median-dispersion/GMT-Geiger-Counter/Firmware/GMT-Geiger-Counter/MelodyAlarm.cpp

#include "Melody.h"

const NonBlockingMelody::Note notes[18] = {
  
  {BUZZER_FREQUENCY_HERTZ, 100},
  {0, 50},
  {BUZZER_FREQUENCY_HERTZ, 100},
  {0, 50},
  {BUZZER_FREQUENCY_HERTZ, 100},
  {0, 200},

  {BUZZER_FREQUENCY_HERTZ, 400},
  {0, 50},
  {BUZZER_FREQUENCY_HERTZ, 400},
  {0, 50},
  {BUZZER_FREQUENCY_HERTZ, 400},
  {0, 200},

  {BUZZER_FREQUENCY_HERTZ, 100},
  {0, 50},
  {BUZZER_FREQUENCY_HERTZ, 100},
  {0, 50},
  {BUZZER_FREQUENCY_HERTZ, 100},
  {0, 400}
  
};

Melody MELODY_ALARM = {notes, 18, 1};
