median-dispersion/GMT-Geiger-Counter/Firmware/GMT-Geiger-Counter/ScreenGeigerCounter.cpp

#include "ScreenGeigerCounter.h"

// ------------------------------------------------------------------------------------------------
// Public

// ================================================================================================
// Constructor
// ================================================================================================
ScreenGeigerCounter::ScreenGeigerCounter():

  // Initialize members

  geigerCounterSetting(2, 31, 160, 129),

  audioSettings(          163, 31,  51, 51, IMAGE_VOLUME  ),
  displaySettings(        215, 31,  51, 51, IMAGE_DISPLAY ),
  goToSleep(              267, 31,  51, 51, IMAGE_SLEEP   ),
  decreaseIntegrationTime(163, 83,  51, 51, IMAGE_DECREASE),
  resetIntegrationTime(   215, 83,  51, 51, IMAGE_RESET   ),
  increaseIntegrationTime(267, 83,  51, 51, IMAGE_INCREASE),
  cosmicRayDetector(      163, 135, 51, 51, IMAGE_MUON    ),
  radiationHistory(       215, 135, 51, 51, IMAGE_HISTORY ),
  trueRNG(                267, 135, 51, 51, IMAGE_DICE    ),
  hotspotSettings(        163, 187, 51, 51, IMAGE_HOTSPOT ),
  wifiSettings(           215, 187, 51, 51, IMAGE_WIFI    ),
  systemSettings(         267, 187, 51, 51, IMAGE_SETTINGS),
  
  _equivalentDoseString("0.00"),
  _countsPerMinuteString("0 CPM"),
  _integrationTimeString("30 s"),

  _equivalentDoseScreen(2, 31, 160, 129, COLOR_GREEN_MEDIUM, COLOR_GREEN_DARK, _equivalentDoseString.c_str(), STRING_MICRO_SIEVERTS_PER_HOUR_ABBREVIATION),
  _radiationRating(2, 161, 160, IMAGE_RADIATION, STRING_NORMAL                 ),
  _countsPerMinute(2, 187, 160, IMAGE_PARTICLE,  _countsPerMinuteString.c_str()),
  _integrationTime(2, 213, 160, IMAGE_CLOCK,     _integrationTimeString.c_str())

{}

// ================================================================================================
// Update
// ================================================================================================
void ScreenGeigerCounter::update(const XPT2046::Point &position) {

  // Update screen elements
  audioSettings.update(position);
  displaySettings.update(position);
  goToSleep.update(position);
  decreaseIntegrationTime.update(position);
  resetIntegrationTime.update(position);
  increaseIntegrationTime.update(position);
  cosmicRayDetector.update(position);
  radiationHistory.update(position);
  trueRNG.update(position);
  hotspotSettings.update(position);
  wifiSettings.update(position);
  systemSettings.update(position);
  geigerCounterSetting.update(position);

}

// ================================================================================================
// Draw
// ================================================================================================
void ScreenGeigerCounter::draw(GFXcanvas16 &canvas) {

  // Clear framebuffer
  canvas.fillScreen(COLOR_BLACK);

  // Draw screen border
  canvas.drawRect(0, 29, 320, 211, COLOR_WHITE);

  // Draw title bar
  canvas.drawRect(0, 0, 320, 30, COLOR_WHITE);
  canvas.fillRect(1, 1, 318, 28, COLOR_GRAY_DARK);

  // Draw title text
  canvas.setFont(&FreeSans9pt7b);
  canvas.setTextColor(COLOR_WHITE);
  canvas.setCursor(5, 20);
  canvas.print(STRING_BETA_GAMMA_GMT_GEIGER_COUNTER);

  // Draw screen elements
  audioSettings.draw(canvas);
  displaySettings.draw(canvas);
  goToSleep.draw(canvas);
  decreaseIntegrationTime.draw(canvas);
  resetIntegrationTime.draw(canvas);
  increaseIntegrationTime.draw(canvas);
  cosmicRayDetector.draw(canvas);
  radiationHistory.draw(canvas);
  trueRNG.draw(canvas);
  hotspotSettings.draw(canvas);
  wifiSettings.draw(canvas);
  systemSettings.draw(canvas);
  _equivalentDoseScreen.draw(canvas);
  _radiationRating.draw(canvas);
  _countsPerMinute.draw(canvas);
  _integrationTime.draw(canvas);

}

// ================================================================================================
// Set the equivalent dose
// ================================================================================================
void ScreenGeigerCounter::setEquivalentDose(const double &equivalentDose) {

  // If equivalent dose value is less than 1000
  if (equivalentDose < 1000) {

    // Convert equivalent dose to a string
    _equivalentDoseString = equivalentDose;

  // If equivalent dose value is more than 1000
  } else {

    // Drop decimal places and convert to string
    _equivalentDoseString = (uint64_t)(round(equivalentDose));

  }

}

// ================================================================================================
// Set the equivalent dose unit
// ================================================================================================
void ScreenGeigerCounter::setEquivalentDoseUnit(GeigerCounter::EquivalentDoseUnit equivalentDoseUnit) {

  // Depending on the equivalent dose unit selected
  // Set the equivalent dose unit string

  switch (equivalentDoseUnit) {

    case GeigerCounter::MICRO_SIEVERTS_PER_HOUR: _equivalentDoseScreen.setUnit(STRING_MICRO_SIEVERTS_PER_HOUR_ABBREVIATION); break;
    case GeigerCounter::MILLI_SIEVERTS_PER_HOUR: _equivalentDoseScreen.setUnit(STRING_MILLI_SIEVERTS_PER_HOUR_ABBREVIATION); break;
    case GeigerCounter::SIEVERTS_PER_HOUR:       _equivalentDoseScreen.setUnit(STRING_SIEVERTS_PER_HOUR_ABBREVIATION);       break;

    case GeigerCounter::MICRO_REM_PER_HOUR: _equivalentDoseScreen.setUnit(STRING_MICRO_REM_PER_HOUR_ABBREVIATION); break;
    case GeigerCounter::MILLI_REM_PER_HOUR: _equivalentDoseScreen.setUnit(STRING_MILLI_REM_PER_HOUR_ABBREVIATION); break;
    case GeigerCounter::REM_PER_HOUR:       _equivalentDoseScreen.setUnit(STRING_REM_PER_HOUR_ABBREVIATION);       break;

    case GeigerCounter::MICRO_RONTGEN_PER_HOUR: _equivalentDoseScreen.setUnit(STRING_MICRO_RONTGEN_PER_HOUR_ABBREVIATION); break;
    case GeigerCounter::MILLI_RONTGEN_PER_HOUR: _equivalentDoseScreen.setUnit(STRING_MILLI_RONTGEN_PER_HOUR_ABBREVIATION); break;
    case GeigerCounter::RONTGEN_PER_HOUR:       _equivalentDoseScreen.setUnit(STRING_RONTGEN_PER_HOUR_ABBREVIATION);       break;

    case GeigerCounter::MICRO_GRAY_PER_HOUR: _equivalentDoseScreen.setUnit(STRING_MICRO_GRAY_PER_HOUR_ABBREVIATION); break;
    case GeigerCounter::MILLI_GRAY_PER_HOUR: _equivalentDoseScreen.setUnit(STRING_MILLI_GRAY_PER_HOUR_ABBREVIATION); break;
    case GeigerCounter::GRAY_PER_HOUR:       _equivalentDoseScreen.setUnit(STRING_GRAY_PER_HOUR_ABBREVIATION);       break;

  }

}

// ================================================================================================
// Set the radiation rating
// ================================================================================================
void ScreenGeigerCounter::setRadiationRating(const GeigerCounter::RadiationRating radiationRating) {

  // Depending on the radiation rating
  // Update the dose screen border and background color
  // Update the radiation rating info box value
  
  switch (radiationRating) {

    case GeigerCounter::RATING_NORMAL:
      _equivalentDoseScreen.setBorderColor(COLOR_GREEN_MEDIUM);
      _equivalentDoseScreen.setBackgroundColor(COLOR_GREEN_DARK);
      _radiationRating.setValue(STRING_NORMAL);
    break;

    case GeigerCounter::RATING_ELEVATED:
      _equivalentDoseScreen.setBorderColor(COLOR_LIME_MEDIUM);
      _equivalentDoseScreen.setBackgroundColor(COLOR_LIME_DARK);
      _radiationRating.setValue(STRING_ELEVATED);
    break;

    case GeigerCounter::RATING_MEDIUM:
      _equivalentDoseScreen.setBorderColor(COLOR_YELLOW_MEDIUM);
      _equivalentDoseScreen.setBackgroundColor(COLOR_YELLOW_DARK);
      _radiationRating.setValue(STRING_MEDIUM);
    break;

    case GeigerCounter::RATING_HIGH:
      _equivalentDoseScreen.setBorderColor(COLOR_RED_MEDIUM);
      _equivalentDoseScreen.setBackgroundColor(COLOR_RED_DARK);
      _radiationRating.setValue(STRING_HIGH);
    break;

    case GeigerCounter::RATING_EXTREME:
      _equivalentDoseScreen.setBorderColor(COLOR_RED_MEDIUM);
      _equivalentDoseScreen.setBackgroundColor(COLOR_RED_DARK);
      _radiationRating.setValue(STRING_EXTREME);
    break;

  }

}


// ================================================================================================
// Set the counts per minute
// ================================================================================================
void ScreenGeigerCounter::setCountsPerMinute(const double &countsPerMinute) {

  // Convert counts per minute to a string with unit appended to it
  _countsPerMinuteString  = (uint64_t)(round(countsPerMinute));
  _countsPerMinuteString += " ";
  _countsPerMinuteString += STRING_COUNTS_PER_MINUTE_ABBREVIATION;

}

// ================================================================================================
// Set the integration time
// ================================================================================================
void ScreenGeigerCounter::setIntegrationTime(const uint8_t integrationTime) {
  
  // Convert integration time to a string with unit appended to it
  _integrationTimeString  = integrationTime;
  _integrationTimeString += " ";
  _integrationTimeString += STRING_SECONDS_ABBREVIATION;

}
