median-dispersion/GMT-Geiger-Counter/Firmware/GMT-Geiger-Counter/ImageDiagram.cpp

#include "Graphics.h"

const PROGMEM uint8_t data[] = {

  "F)F)F)F)F)F)F)F)F)F)F)F)F)F)F)F)F)F)F)F)F)F)F)F)F)F)F)F)F)F)F)F)F)F)F)F)"
  "F)F)F)F)F)F)F)F)F)F)F)F)\377\377F)F)F)F)F)F)F)F)F)F)F)F)F)F)F)F)F)F)F)F)"
  "F)F)F)F)F)F)F)F)F)F)F)F)F)F)F)F)F)F)F)F)F)F)F)F)F)F)F)F)F)F)F)F)F)F)F)F)"
  "F)F)F)F)F)F)F)F)F)F)F)F)F)F)F)F)F)F)F)F)F)F)F)F)F)F)F)F)F)F)F)F)F)F)F)F)"
  "F)F)F)F)\377\377F)F)F)F)F)F)F)F)F)F)F)F)F)F)F)F)F)F)F)F)F)F)F)F)F)F)F)F)"
  "F)F)F)F)F)F)F)F)F)F)F)F)F)F)F)F)F)F)F)F)F)F)F)F)F)F)F)F)F)F)F)F)F)F)F)F)"
  "F)F)F)F)F)F)F)F)F)F)F)F)F)F)F)F)F)F)F)F)F)F)F)F)F)F)F)F)F)F)F)F)\377\377"
  "F)F)F)F)F)F)F)F)F)F)F)F)F)F)F)F)F)F)F)F)F)F)F)F)F)F)F)F)F)F)F)F)F)F)F)F)"
  "F)F)F)F)F)F)F)F)F)F)F)F)F)F)F)F)F)F)F)F)F)F)F)F)F)F)F)F)F)F)F)F)F)F)F)F)"
  "F)F)F)F)F)F)F)F)F)F)F)F)F)F)F)F)F)F)F)F)F)F)F)F)\377\377F)F)F)F)F)F)F)F)"
  "F)F)F)F)F)F)F)F)F)F)F)F)F)F)F)F)F)F)F)F)F)F)F)F)F)F)F)F)F)F)F)F)F)F)F)F)"
  "F)F)F)F)F)F)F)F)F)F)F)F)F)F)F)F)F)F)F)F)F)F)F)F)F)F)F)F)F)F)F)F)F)F)F)F)"
  "F)F)F)F)F)F)F)F)F)F)F)F)F)F)F)F)\377\377F)F)F)F)F)F)F)F)F)F)F)F)F)F)F)F)"
  "F)F)F)F)F)F)F)F)F)F)F)F)F)F)F)F)F)F)F)F)F)F)F)F)F)F)F)F)F)F)F)F)F)F)F)F)"
  "F)F)F)F)F)F)F)F)F)F)F)F)F)F)F)F)F)F)F)F)F)F)F)F)F)F)F)F)F)F)F)F)F)F)F)F)"
  "F)F)F)F)F)F)F)F)\377\377F)F)F)F)F)F)F)F)F)F)F)F)F)F)F)F)F)F)F)F)F)F)F)F)"
  "F)F)F)F)F)F)F)F)F)F)F)F)F)F)F)F)F)F)F)F)F)F)F)F)F)F)F)F)F)F)F)F)F)F)F)F)"
  "F)F)F)F)F)F)F)F)F)F)F)F)F)F)F)F)F)F)F)F)F)F)F)F)F)F)F)F)F)F)F)F)F)F)F)F)"
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
  "\265\070\306\314Z\314Z\314Z\314Z\314Z\314Z\314Z\314Z\314Z\314Z\314Z\314Z\314"
  "Z\314Z\314Z\314Z\314Z\314Z\314Z\314Z\314Z\314Z\314Z\314Z\314Z\314Z\314Z\377"
  "\377\377\377\377\377\377\377\377\377\377\377\377\377\323\234F)\323\234\377"
  "\377\314Z\314Z\314Z\314Z\314Z\314Z\377\377\314Z\314Z\314Z\314Z\314Z\314Z"
  "\314Z\314Z\314Z\314Z\314Z\314Z\314Z\314Z\314Z\314Z\314Z\314Z\314Z\314Z\314"
  "Z\314Z\314Z\314Z\314Z\314Z\314Z\222\224\276\367Y\316\314Z\314Z\257s\276\367"
  "\333\336\314Z\314Z\034\347=\347\327\275\314Z\314Z\314Z\337\377\314Z\222\224"
  "\276\367\333\336\314Z\314Z\226\265\070\306\314Z\314Z\314Z\314Z\314Z\314Z\314"
  "Z\314Z\314Z\314Z\314Z\314Z\314Z\314Z\314Z\314Z\314Z\314Z\314Z\314Z\314Z\314"
  "Z\314Z\314Z\314Z\314Z\314Z\377\377\314Z\314Z\314Z\314Z\314Z\314Z\377\377"
  "\323\234\377\377\314Z\314Z\314Z\314Z\314Z\314Z\314Z\377\377\314Z\314Z\314"
  "Z\314Z\314Z\314Z\314Z\314Z\314Z\314Z\314Z\314Z\314Z\314Z\314Z\314Z\314Z\314"
  "Z\314Z\314Z\314Z\314Z\314Z\314Z\314Z\314Z\314Z\222\224\373\336]\357\314Z"
  "\314Z\226\265\272\326\333\336\314Z\216s\236\367\364\234<\347\314Z\314Z\314"
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
  "Z\314Z\314Z\314Z\314Z\314Z\314Z\222\224\373\336Mk<\347\064\245\030\306\222"
  "\224\333\336nk\377\377\377\377\377\377\377\377\373\336\314Z\314Z\337\377"
  "\314Z\222\224\373\336\314Z\216s\236\367\367\275\070\306\314Z\314Z\314Z\314"
  "Z\314Z\314Z\314Z\314Z\314Z\314Z\314Z\314Z\314Z\314Z\314Z\314Z\314Z\314Z\314"
  "Z\314Z\314Z\314Z\314Z\314Z\314Z\314Z\314Z\377\377\314Z\314Z\314Z\314Z\314"
  "Z\314Z\314Z\377\377\323\234\377\377\314Z\314Z\314Z\314Z\314Z\314Z\377\377"
  "\314Z\314Z\314Z\314Z\314Z\314Z\314Z\314Z\314Z\314Z\314Z\314Z\314Z\314Z\314"
  "Z\314Z\314Z\314Z\314Z\314Z\314Z\314Z\314Z\314Z\314Z\314Z\314Z\222\224\373"
  "\336\314Z\373\336\374\336r\214\222\224\333\336v\255\373\336\314Z\314Z\317"
  "{\337\377Nk\314Z\337\377\314Z\222\224\373\336\314Z\314Z\267\265\276\367\070"
  "\306\314Z\314Z\314Z\314Z\314Z\314Z\314Z\314Z\314Z\314Z\314Z\314Z\314Z\314"
  "Z\314Z\314Z\314Z\314Z\314Z\314Z\314Z\314Z\314Z\314Z\314Z\314Z\314Z\377\377"
  "\314Z\314Z\314Z\314Z\314Z\314Z\377\377\323\234\304\030\323\234\377\377\377"
  "\377\377\377\377\377\377\377\377\377\377\377\314Z\314Z\314Z\314Z\314Z\314"
  "Z\314Z\314Z\314Z\314Z\314Z\314Z\314Z\314Z\314Z\314Z\314Z\314Z\314Z\314Z\314"
  "Z\314Z\314Z\314Z\314Z\314Z\314Z\222\224\373\336\314Z\266\265\236\367\314"
  "Z\222\224\333\336\333\336U\255\314Z\314Z\314Z\034\347u\255\314Z\337\377\314"
  "Z\222\224\373\336\314Z\314Z\354Z]\357\070\306\314Z\314Z\314Z\314Z\314Z\314"
  "Z\314Z\314Z\314Z\314Z\314Z\314Z\314Z\314Z\314Z\314Z\314Z\314Z\314Z\314Z\314"
  "Z\314Z\314Z\314Z\314Z\314Z\314Z\377\377\377\377\377\377\377\377\377\377\377"
  "\377\377\377\323\234\304\030\304\030\304\030\304\030\304\030\304\030\304\030\304"
  "\030\304\030\377\377\314Z\314Z\314Z\314Z\314Z\314Z\314Z\314Z\314Z\314Z\314"
  "Z\314Z\314Z\314Z\314Z\314Z\314Z\314Z\314Z\314Z\314Z\314Z\314Z\314Z\314Z\314"
  "Z\314Z\314Z\314Z\314Z\314Z\314Z\314Z\314Z\314Z\314Z\314Z\314Z\314Z\314Z\314"
  "Z\314Z\314Z\314Z\314Z\314Z\314Z\314Z\314Z\314Z\314Z\314Z\314Z\314Z\314Z\314"
  "Z\314Z\314Z\314Z\314Z\314Z\314Z\314Z\314Z\314Z\314Z\314Z\314Z\314Z\314Z\314"
  "Z\314Z\314Z\314Z\314Z\314Z\314Z\314Z\314Z\377\377\304\030\304\030\304\030\304"
  "\030\304\030\304\030\304\030\304\030F)\304\030\304\030\304\030\304\030\304\030\304"
  "\030\304\030\323\234\064\245\314Z\314Z\314Z\314Z\314Z\314Z\314Z\314Z\314Z\314"
  "Z\314Z\314Z\314Z\314Z\314Z\314Z\314Z\314Z\314Z\314Z\314Z\314Z\314Z\314Z\314"
  "Z\314Z\314Z\314Z\314Z\314Z\314Z\314Z\314Z\314Z\314Z\314Z\314Z\314Z\314Z\314"
  "Z\314Z\314Z\314Z\314Z\314Z\314Z\314Z\314Z\314Z\314Z\314Z\314Z\314Z\314Z\314"
  "Z\314Z\314Z\314Z\314Z\314Z\314Z\314Z\314Z\314Z\314Z\314Z\314Z\314Z\314Z\314"
  "Z\314Z\314Z\314Z\314Z\314Z\314Z\314Z\064\245\323\234\304\030\304\030\304\030"
  "\304\030\304\030\304\030\304\030F)F)F)F)F)F)F)F)\304\030\304\030\323\234\377\377"
  "\377\377\377\377\377\377\377\377\377\377\377\377\377\377\377\377\377\377"
  "\377\377\377\377\377\377\377\377\377\377\377\377\377\377\377\377\377\377"
  "\377\377\377\377\377\377\377\377\377\377\377\377\377\377\377\377\377\377"
  "\377\377\377\377\377\377\377\377\377\377\377\377\377\377\377\377\377\377"
  "\377\377\377\377\377\377\377\377\377\377\377\377\377\377\377\377\377\377"
  "\377\377\377\377\377\377\377\377\377\377\377\377\377\377\377\377\377\377"
  "\377\377\377\377\377\377\377\377\377\377\377\377\377\377\377\377\377\377"
  "\377\377\377\377\377\377\377\377\377\377\377\377\377\377\377\377\377\377"
  "\377\377\377\377\377\377\377\377\323\234\304\030\304\030F)F)F)F)F)F)F)F)F)"
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
  "Z\314Z\314Z\314Z\314Z\314Z\314Z\314Z\314Z\314Z\314Z\314Z\314Z\314Z\314Z\314"
  "Z\314Z\314Z\314Z\314Z\314Z\314Z\314Z\314Z\314Z\314Z\314Z\314Z\314Z\314Z\314"
  "Z\314Z\314Z\314Z\314Z\314Z\314Z\314Z\314Z\314Z\314Z\314Z\314Z\064\245\323"
  "\234F)F)F)F)F)F)F)F)F)F)F)F)F)F)F)F)\377\377\314Z\314Z\314Z\314Z\314Z\314"
  "Z\314Z\314Z\314Z\314Z\314Z\314Z\314Z\314Z\314Z\314Z\314Z\314Z\314Z\314Z\314"
  "Z\314Z\314Z\314Z\314Z\314Z\314Z\314Z\314Z\314Z\314Z\314Z\314Z\314Z\314Z\314"
  "Z\314Z\314Z\314Z\314Z\314Z\314Z\314Z\314Z\314Z\314Z\314Z\314Z\314Z\314Z\314"
  "Z\314Z\314Z\314Z\314Z\314Z\314Z\314Z\314Z\314Z\314Z\314Z\314Z\314Z\314Z\314"
  "Z\314Z\314Z\314Z\314Z\314Z\314Z\314Z\314Z\314Z\314Z\314Z\314Z\314Z\377\377"
  "F)F)F)F)F)F)F)F)F)\323\234\377\377\377\377\377\377\377\377\377\377\377\377"
  "\377\377\314Z\314Z\314Z\314Z\314Z\314Z\314Z\314Z\314Z\314Z\314Z\222\224\377"
  "\377\377\377\377\377\377\377\373\336\314Z\317{\333\336\337\377\276\367\232"
  "\326Nk\314Z\222\224\034\347\314Z\314Z\314Z\314Z\222\224\034\347\314Z\314Z\314"
  "Z\314Z\314Z\317{\333\336\337\377\276\367\232\326Nk\314Z\034\347\024\245\314"
  "Z\314Z\276\367\064\245\314Z\314Z\276\367\064\245\377\377\377\377\377\377\377"
  "\377}\357\222\224\377\377\377\377\377\377\337\377Y\316\314Z\314Z\314Z\314"
  "Z\314Z\314Z\314Z\314Z\314Z\314Z\314Z\314Z\314Z\377\377\377\377\377\377\377"
  "\377\377\377\377\377\377\377\323\234F)\323\234\377\377\314Z\314Z\314Z\314"
  "Z\314Z\314Z\377\377\314Z\314Z\314Z\314Z\314Z\314Z\314Z\314Z\314Z\314Z\314"
  "Z\222\224\034\347\314Z\314Z\314Z\314Z\314Z]\357\030\306\217s\320{\232\326\333"
  "\336\314Z\222\224\034\347\314Z\314Z\314Z\314Z\222\224\034\347\314Z\314Z\314"
  "Z\314Z\314Z]\357\030\306\217s\320{\232\326\333\336\314Z\030\306\070\306\314"
  "Zr\214\377\377Y\316\314Z\360{\236\367\222\224\034\347\314Z\314Z\314Z\314Z"
  "\222\224\034\347\314Z\314Z\317{}\357\263\224\314Z\314Z\314Z\314Z\314Z\314"
  "Z\314Z\314Z\314Z\314Z\314Z\314Z\377\377\314Z\314Z\314Z\314Z\314Z\314Z\377"
  "\377\323\234\377\377\314Z\314Z\314Z\314Z\314Z\314Z\314Z\377\377\314Z\314"
  "Z\314Z\314Z\314Z\314Z\314Z\314Z\314Z\314Z\314Z\222\224\034\347\314Z\314Z\314"
  "Z\314Z\065\245\333\336\314Z\314Z\314Z\314Z}\357Q\214\222\224\034\347\314Z\314"
  "Z\314Z\314Z\222\224\034\347\314Z\314Z\314Z\314Z\065\245\333\336\314Z\314Z\314"
  "Z\314Z}\357Q\214\364\234\373\336\314Z\327\275\034\347]\357\314Z\065\245\272"
  "\326\222\224\034\347\314Z\314Z\314Z\314Z\222\224\034\347\314Z\314Z\314Z\272"
  "\326U\255\314Z\314Z\314Z\314Z\314Z\314Z\314Z\314Z\314Z\314Z\314Z\314Z\377"
  "\377\314Z\314Z\314Z\314Z\314Z\314Z\314Z\377\377\377\377\314Z\314Z\314Z\314"
  "Z\314Z\314Z\314Z\377\377\314Z\314Z\314Z\314Z\314Z\314Z\314Z\314Z\314Z\314"
  "Z\314Z\222\224\377\377\377\377\377\377\377\377\222\224\070\306\266\265\314"
  "Z\314Z\314Z\314Zy\316u\255\222\224\034\347\314Z\314Z\314Z\314Z\222\224\034"
  "\347\314Z\314Z\314Z\314Z\070\306\266\265\314Z\314Z\314Z\314Zy\316u\255Mk\276"
  "\367\314Z\333\336\364\234\276\367nk\071\306\266\265\222\224\377\377\377\377"
  "\377\377\377\377\373\336\222\224\034\347\314Z\314Z\317{}\357\020\204\314Z\314"
  "Z\314Z\314Z\314Z\314Z\314Z\314Z\314Z\314Z\314Z\314Z\377\377\314Z\314Z\314"
  "Z\314Z\314Z\314Z\314Z\377\377\377\377\314Z\314Z\314Z\314Z\314Z\314Z\314Z"
  "\377\377\314Z\314Z\314Z\314Z\314Z\314Z\314Z\314Z\314Z\314Z\314Z\222\224\034"
  "\347\314Z\314Z\314Z\314Z\070\306\266\265\314Z\314Z\314Z\314ZY\316v\255\222"
  "\224\034\347\314Z\314Z\314Z\314Z\222\224\034\347\314Z\314Z\314Z\314Z\070\306"
  "\266\265\314Z\314Z\314Z\314ZY\316v\255\314Z]\357\360{\236\367\015c\272\326"
  "\064\245\034\347Q\214\222\224\034\347\314Z\314Z\314Z\314Z\222\224\377\377\377"
  "\377\377\377\377\377z\316\314Z\314Z\314Z\314Z\314Z\314Z\314Z\314Z\314Z\314"
  "Z\314Z\314Z\314Z\377\377\314Z\314Z\314Z\314Z\314Z\314Z\314Z\377\377\377\377"
  "\314Z\314Z\314Z\314Z\314Z\314Z\314Z\377\377\314Z\314Z\314Z\314Z\314Z\314"
  "Z\314Z\314Z\314Z\314Z\314Z\222\224\034\347\314Z\314Z\314Z\314Z\065\245\333"
  "\336\314Z\314Z\314Z\314Z]\357r\214\222\224\034\347\314Z\314Z\314Z\314Z\222"
  "\224\034\347\314Z\314Z\314Z\314Z\065\245\333\336\314Z\314Z\314Z\314Z]\357r"
  "\214\314Zy\316\070\306\034\347\314Zu\255Y\316\236\367\314Z\222\224\034\347\314"
  "Z\314Z\314Z\314Z\222\224\034\347\314Z\314Z\217s~\357\020\204\314Z\314Z\314"
  "Z\314Z\314Z\314Z\314Z\314Z\314Z\314Z\314Z\314Z\377\377\314Z\314Z\314Z\314"
  "Z\314Z\314Z\314Z\377\377\323\234\377\377\314Z\314Z\314Z\314Z\314Z\314Z\377"
  "\377\314Z\314Z\314Z\314Z\314Z\314Z\314Z\314Z\314Z\314Z\314Z\222\224\034\347"
  "\314Z\314Z\314Z\314Z\314Z]\357\030\306\217s\317{\232\326\373\336\314Z\222"
  "\224\034\347\314Z\314Z\314Z\314Z\222\224\034\347\314Z\314Z\314Z\314Z\314Z]"
  "\357\030\306\217s\317{\232\326\373\336\314Z\314ZU\255\276\367\367\275\314"
  "Z\217s\276\367\374\336\314Z\222\224\034\347\314Z\314Z\314Z\314Z\222\224\034"
  "\347\314Z\314Z\314Z\333\336\263\224\314Z\314Z\314Z\314Z\314Z\314Z\314Z\314"
  "Z\314Z\314Z\314Z\314Z\377\377\314Z\314Z\314Z\314Z\314Z\314Z\377\377\323\234"
  "\304\030\323\234\377\377\377\377\377\377\377\377\377\377\377\377\377\377\314"
  "Z\314Z\314Z\314Z\314Z\314Z\314Z\314Z\314Z\314Z\314Z\222\224\034\347\314Z\314"
  "Z\314Z\314Z\314Z\317{\333\336\337\377\337\377\232\326Nk\314Z\222\224\377"
  "\377\377\377\377\377\377\377U\255\222\224\377\377\377\377\377\377\377\377"
  "U\255\314Z\317{\333\336\337\377\337\377\232\326Nk\314Z\314Z\317{\377\377"
  "Q\214\314Z\314Z]\357\030\306\314Z\222\224\377\377\377\377\377\377\377\377"
  "\377\377\263\224\034\347\314Z\314Z\314Zz\316\327\275\314Z\314Z\314Z\314Z\314"
  "Z\314Z\314Z\314Z\314Z\314Z\314Z\314Z\377\377\377\377\377\377\377\377\377"
  "\377\377\377\377\377\323\234\304\030\304\030\304\030\304\030\304\030\304\030\304"
  "\030\304\030\304\030\377\377\314Z\314Z\314Z\314Z\314Z\314Z\314Z\314Z\314Z\314"
  "Z\314Z\314Z\314Z\314Z\314Z\314Z\314Z\314Z\314Z\314Z\314Z\314Z\314Z\314Z\314"
  "Z\314Z\314Z\314Z\314Z\314Z\314Z\314Z\314Z\314Z\314Z\314Z\314Z\314Z\314Z\314"
  "Z\314Z\314Z\314Z\314Z\314Z\314Z\314Z\314Z\314Z\314Z\314Z\314Z\314Z\314Z\314"
  "Z\314Z\314Z\314Z\314Z\314Z\314Z\314Z\314Z\314Z\314Z\314Z\314Z\314Z\314Z\314"
  "Z\314Z\314Z\314Z\314Z\314Z\314Z\314Z\314Z\314Z\377\377\304\030\304\030\304"
  "\030\304\030\304\030\304\030\304\030\304\030F)\304\030\304\030\304\030\304\030\304"
  "\030\304\030\304\030\323\234\064\245\314Z\314Z\314Z\314Z\314Z\314Z\314Z\314Z"
  "\314Z\314Z\314Z\314Z\314Z\314Z\314Z\314Z\314Z\314Z\314Z\314Z\314Z\314Z\314"
  "Z\314Z\314Z\314Z\314Z\314Z\314Z\314Z\314Z\314Z\314Z\314Z\314Z\314Z\314Z\314"
  "Z\314Z\314Z\314Z\314Z\314Z\314Z\314Z\314Z\314Z\314Z\314Z\314Z\314Z\314Z\314"
  "Z\314Z\314Z\314Z\314Z\314Z\314Z\314Z\314Z\314Z\314Z\314Z\314Z\314Z\314Z\314"
  "Z\314Z\314Z\314Z\314Z\314Z\314Z\314Z\314Z\314Z\064\245\323\234\304\030\304"
  "\030\304\030\304\030\304\030\304\030\304\030F)F)F)F)F)F)F)F)\304\030\304\030\323"
  "\234\377\377\377\377\377\377\377\377\377\377\377\377\377\377\377\377\377"
  "\377\377\377\377\377\377\377\377\377\377\377\377\377\377\377\377\377\377"
  "\377\377\377\377\377\377\377\377\377\377\377\377\377\377\377\377\377\377"
  "\377\377\377\377\377\377\377\377\377\377\377\377\377\377\377\377\377\377"
  "\377\377\377\377\377\377\377\377\377\377\377\377\377\377\377\377\377\377"
  "\377\377\377\377\377\377\377\377\377\377\377\377\377\377\377\377\377\377"
  "\377\377\377\377\377\377\377\377\377\377\377\377\377\377\377\377\377\377"
  "\377\377\377\377\377\377\377\377\377\377\377\377\377\377\377\377\377\377"
  "\377\377\377\377\377\377\377\377\377\377\377\323\234\304\030\304\030F)F)F)"
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
  "F)F)F)F)F)F)F)F)F)F)F)F)F)F)F)F)F)F)F)F)F)F)F)F)F)F)F)F)F)F)F)F)F)F)F)F)"
  "F)F)F)F)F)F)F)F)F)F)F)F)F)\313ZF)F)F)F)F)F)F)F)F)F)F)F)F)F)F)F)F)F)F)F)F"
  ")F)F)F)F)F)F)F)F)F)F)F)F)F)F)F)F)F)F)F)F)F)F)F)F)F)F)F)"

};

Image IMAGE_DIAGRAM = {97, 99, (const uint16_t*)(data)};
