median-dispersion/GMT-Geiger-Counter/Firmware/GMT-Geiger-Counter/ImageDice.cpp

#include "Graphics.h"

const PROGMEM uint8_t data[] = {

  "\314Z\314Z\015c\065\245\327\275\370\275\370\275\370\275\370\275\370\275\370"
  "\275\370\275\370\275\370\275\370\275\370\275\370\275\370\275\370\275\370"
  "\275\370\275\370\275\370\275\370\275\370\275\370\275\370\275\370\275\370"
  "\275\370\275\370\275\370\275\327\275\065\245\015c\314Z\314Z\314Z\061\204}\357"
  "\377\377\377\377\377\377\377\377\377\377\377\377\377\377\377\377\377\377"
  "\377\377\377\377\377\377\377\377\377\377\377\377\377\377\377\377\377\377"
  "\377\377\377\377\377\377\377\377\377\377\377\377\377\377\377\377\377\377"
  "\377\377\377\377\377\377\377\377}\357\061\204\314Z\015c}\357\377\377\377\377"
  "\377\377\377\377\377\377\377\377\377\377\377\377\377\377\377\377\377\377"
  "\377\377\377\377\377\377\377\377\377\377\377\377\377\377\377\377\377\377"
  "\377\377\377\377\377\377\377\377\377\377\377\377\377\377\377\377\377\377"
  "\377\377\377\377\377\377\377\377}\357\015c\064\245\377\377\377\377\377\377"
  "\377\377\377\377\377\377\377\377\377\377\377\377\377\377\377\377\377\377"
  "\377\377\377\377\377\377\377\377\377\377\377\377\377\377\377\377\377\377"
  "\377\377\377\377\377\377\377\377\377\377\377\377\377\377\377\377\377\377"
  "\377\377\377\377\377\377\377\377\377\377\024\245\327\275\377\377\377\377\377"
  "\377\377\377\377\377\377\377\377\377\377\377\377\377\377\377\377\377\377"
  "\377\377\377\377\377\377\377\377\377\377\377\377\377\377\377\377\377\377"
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
  "\377\377\377\377\377\377\377\377\377\377\377\377\377\377\377\377\377\377"
  "\377\327\275\327\275\377\377\377\377\377\377\377\377\377\377\377\377\377"
  "\377\377\377\377\377\377\377\377\377\377\377\377\377\377\377\377\377\377"
  "\377\377\377\377\377\377\377\377\377\377\377\377\377\377\377\377\377\377"
  "\377\377\377\377\377\377\377\377\377\377\377\377\377\377\377\377\377\377"
  "\377\377\377\327\275\064\245\377\377\377\377\377\377\377\377\377\377\377\377"
  "\377\377\377\377\377\377\377\377\377\377\377\377\377\377\377\377\377\377"
  "\377\377\377\377\377\377\377\377\377\377\377\377\377\377\377\377\377\377"
  "\377\377\377\377\377\377\377\377\377\377\377\377\377\377\377\377\377\377"
  "\377\377\377\377\024\245\015c}\357\377\377\377\377\377\377\377\377\377\377"
  "\377\377\377\377\377\377\377\377\377\377\377\377\377\377\377\377\377\377"
  "\377\377\377\377\377\377\377\377\377\377\377\377\377\377\377\377\377\377"
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

};

Image IMAGE_DICE = {37, 37, (const uint16_t*)(data)};
