median-dispersion/GMT-Geiger-Counter/Firmware/GMT-Geiger-Counter/ImageMuon.cpp

#include "Graphics.h"

const PROGMEM uint8_t data[] = {

  "\314Z\314Z\314Z\314Z\314Z\314Z\314Z\314Z\314Z\314Z\314Z\314Z\314Z\314Z\354"
  "ZQ\214\065\245\266\265\267\265\266\265\065\245Q\214\354Z\314Z\314Z\314Z\314"
  "Z\314Z\314Z\314Z\314Z\314Z\314Z\314Z\314Z\314Z\314Z\314Z\314Z\314Z\314Z\314"
  "Z\314Z\314Z\314Z\314Z\314Z\314Znk\226\265\034\347\337\377\377\377\377\377"
  "\377\377\377\377\377\377\377\377\377\377\337\377\034\347\226\265nk\314Z\314"
  "Z\314Z\314Z\314Z\314Z\314Z\314Z\314Z\314Z\314Z\314Z\314Z\314Z\314Z\314Z\314"
  "Z\314Z\314Z\314Z\217sY\316\337\377\377\377\377\377\377\377\377\377\377\377"
  "\377\377\377\377\377\377\377\377\377\377\377\377\377\377\377\377\337\377"
  "Y\316\216s\314Z\314Z\314Z\314Z\314Z\314Z\314Z\314Z\314Z\314Z\314Z\314Z\314"
  "Z\314Z\314Z\314Z\314Z\226\265\337\377\377\377\377\377\377\377\377\377\377"
  "\377\377\377\377\377\377\377\377\377\377\377\377\377\377\377\377\377\377"
  "\377\377\377\377\377\377\377\276\367\226\265\314Z\314Z\314Z\314Z\314Z\314"
  "Z\314Z\314Z\314Z\314Z\314Z\314Z\314Z\314Z-c\333\336\377\377\377\377\377\377"
  "\377\377\377\377\377\377\377\377\377\377\377\377\377\377\377\377\377\377"
  "\377\377\377\377\377\377\377\377\377\377\377\377\377\377\377\377\377\377"
  "\272\326-c\314Z\314Z\314Z\314Z\314Z\314Z\314Z\314Z\314Z\314Z\314Znk<\347"
  "\377\377\377\377\377\377\377\377\377\377\377\377\377\377\377\377\377\377"
  "\377\377\377\377\377\377\377\377\377\377\377\377\377\377\377\377\377\377"
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
  "Z\314Z\314Z\314Z\314Z\314Z\314Z\314Z\314Z\314Z\314Z\314Z\314Z\314Z\314Z\314"
  "Z\314Z\314Z\354Z\061\204\064\245\226\265\267\265\226\265\064\245\061\204\354"
  "Z\314Z\314Z\314Z\314Z\314Z\314Z\314Z\314Z\314Z\314Z\314Z\314Z\314Z\314Z"

};

Image IMAGE_MUON = {37, 37, (const uint16_t*)(data)};
