median-dispersion/GMT-Geiger-Counter/Firmware/GMT-Geiger-Counter/ImageDiceSmall.cpp

#include "Graphics.h"

const PROGMEM uint8_t data[] = {

  "\314Z\314Z\314Z\354Znknknknknknknknknknknknknknknknknknknknknk\354Z\314Z"
  "\314Z\314Z\314Znk\333\336\337\377\377\377\377\377\377\377\377\377\377\377"
  "\377\377\377\377\377\377\377\377\377\377\377\377\377\377\377\377\377\377"
  "\377\377\377\377\377\377\377\377\377\377\377\377\377\377\337\377\333\336"
  "nk\314Z\314Z\333\336\377\377\377\377\377\377\377\377\377\377\377\377\377"
  "\377\377\377\377\377\377\377\377\377\377\377\377\377\377\377\377\377\377"
  "\377\377\377\377\377\377\377\377\377\377\377\377\377\377\377\377\377\377"
  "\377\333\336\314Z\354Z\337\377\377\377\377\377\377\377\377\377\377\377\377"
  "\377\377\377\377\377\377\377\377\377\377\377\377\377\377\377\377\377\377"
  "\377\377\377\377\377\377\377\377\377\377\377\377\377\377\377\377\377\377"
  "\377\377\377\337\377\354ZNk\377\377\377\377\377\377\377\377\377\377\377\377"
  "\377\377\377\377\377\377\377\377\377\377\377\377\377\377\377\377\377\377"
  "\377\377\377\377\377\377\377\377\377\377\377\377\377\377\377\377\377\377"
  "\377\377\377\377\377\377NkNk\377\377\377\377\377\377\377\377\377\377\377"
  "\377\377\377\377\377\377\377\377\377\377\377\377\377\377\377\377\377\377"
  "\377\377\377\377\377\377\377\377\377\377\377\377\377\377\377\377\377\377"
  "\377\377\377\377\377\377\377NkNk\377\377\377\377\377\377\377\377\377\377"
  "\377\377\377\377]\357\276\367\377\377\377\377\377\377\377\377\377\377\377"
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
  "\377\377\377\377\377\377\377\377\377\377\377\377\377\377\377\377\377\377"
  "\377\377\337\377\354Z\314Z\333\336\377\377\377\377\377\377\377\377\377\377"
  "\377\377\377\377\377\377\377\377\377\377\377\377\377\377\377\377\377\377"
  "\377\377\377\377\377\377\377\377\377\377\377\377\377\377\377\377\377\377"
  "\377\377\377\377\333\336\314Z\314Znk\333\336\337\377\377\377\377\377\377"
  "\377\377\377\377\377\377\377\377\377\377\377\377\377\377\377\377\377\377"
  "\377\377\377\377\377\377\377\377\377\377\377\377\377\377\377\377\377\377"
  "\377\337\377\333\336nk\314Z\314Z\314Z\314Z\354Znknknknknknknknknknknknkn"
  "knknknknknknknknk\354Z\314Z\314Z\314Z"

};

Image IMAGE_DICE_SMALL = {29, 29, (const uint16_t*)(data)};
