median-dispersion/GMT-Geiger-Counter/Firmware/GMT-Geiger-Counter/ImageDisplay.cpp

#include "Graphics.h"

const PROGMEM uint8_t data[] = {

  "\314Z\314Z\314Z\314Z\314Z\314Z\314Z\314Z\314Z\314Z\314Z\314Z\314Z\314Z\364"
  "\234<\347\364\234\314Z\314Z\314Z\314Z\314Z\314Z\314Z\314Z\314Z\314Z\314Z"
  "\314Z\314Z\314Z\314Z\314Z\314Z\314Z\314Z\314Z\314Z\314Z\314Z\314Z\314Z\314"
  "Z\314Z\364\234\337\377\377\377\377\377\024\245\314Z\314Z\314Z\314Z\314Z\314"
  "Z\314Z\314Z\314Z\314Z\314Z\314Z\314Z\314Z\314Z\314Z\314Z\314Z\314Z\314Z\314"
  "Z\314Z\314Z\314Z\314Z\364\234\337\377\377\377\377\377\377\377\377\377\024"
  "\245\314Z\314Z\314Z\314Z\314Z\314Z\314Z\314Z\314Z\314Z\314Z\314Z\314Z\314"
  "Z\314Z\314Z\314Z\314Z\314Z\314Z\314Z\314Z\314Z\364\234\337\377\377\377\377"
  "\377\377\377\377\377\377\377\377\377\024\245\314Z\314Z\314Z\314Z\314Z\314"
  "Z\314Z\314Z\314Z\314Z\314Z\314Z\314Z\314Z\314ZQ\214\272\326\333\336\333\336"
  "\333\336\333\336\333\336\337\377\377\377\377\377\377\377\377\377\377\377"
  "\377\377\377\377\337\377\333\336\333\336\333\336\333\336\333\336\272\326"
  "Q\214\314Z\314Z\314Z\314Z\314Z\314Z\314Z\314Z\272\326\377\377\377\377\377"
  "\377\377\377\377\377\377\377\377\377\377\377\377\377\377\377\377\377\377"
  "\377\377\377\377\377\377\377\377\377\377\377\377\377\377\377\377\377\377"
  "\377\272\326\314Z\314Z\314Z\314Z\314Z\314Z\314Z\314Z\272\326\377\377\377"
  "\377\377\377\377\377\377\377\377\377\377\377\377\377\377\377\377\377\377"
  "\377\377\377\377\377\377\377\377\377\377\377\377\377\377\377\377\377\377"
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
  "\377\377\377\377\377\377\377\377\377\377\377\377\377\377\377\377\377\377"
  "\377\377\377\377\377\377\377\377\377\377\377\377\377\377\377\377\377\377"
  "\377\272\326\314Z\314Z\314Z\314Z\314Z\314Z\314Z\314ZQ\214\272\326\333\336"
  "\333\336\333\336\333\336\333\336\337\377\377\377\377\377\377\377\377\377"
  "\377\377\377\377\377\377\337\377\333\336\333\336\333\336\333\336\333\336"
  "\272\326Q\214\314Z\314Z\314Z\314Z\314Z\314Z\314Z\314Z\314Z\314Z\314Z\314"
  "Z\314Z\314Z\314Z\364\234\337\377\377\377\377\377\377\377\377\377\377\377"
  "\377\377\024\245\314Z\314Z\314Z\314Z\314Z\314Z\314Z\314Z\314Z\314Z\314Z\314"
  "Z\314Z\314Z\314Z\314Z\314Z\314Z\314Z\314Z\314Z\314Z\314Z\364\234\337\377"
  "\377\377\377\377\377\377\377\377\024\245\314Z\314Z\314Z\314Z\314Z\314Z\314"
  "Z\314Z\314Z\314Z\314Z\314Z\314Z\314Z\314Z\314Z\314Z\314Z\314Z\314Z\314Z\314"
  "Z\314Z\314Z\314Z\364\234\337\377\377\377\377\377\024\245\314Z\314Z\314Z\314"
  "Z\314Z\314Z\314Z\314Z\314Z\314Z\314Z\314Z\314Z\314Z\314Z\314Z\314Z\314Z\314"
  "Z\314Z\314Z\314Z\314Z\314Z\314Z\314Z\314Z\364\234<\347\364\234\314Z\314Z"
  "\314Z\314Z\314Z\314Z\314Z\314Z\314Z\314Z\314Z\314Z\314Z\314Z"

};

Image IMAGE_DISPLAY = {31, 31, (const uint16_t*)(data)};
