median-dispersion/GMT-Geiger-Counter/Firmware/GMT-Geiger-Counter/ImageSettings.cpp

#include "Graphics.h"

const PROGMEM uint8_t data[] = {

  "\314Z\314Z\314Z\314Z\314Z\314Z\314Z\314Z\314Z\314Z\314ZNk\373\336]\357]\357"
  "]\357]\357]\357\373\336Nk\314Z\314Z\314Z\314Z\314Z\314Z\314Z\314Z\314Z\314"
  "Z\314Z\314Z\314Z\314Z\314Z\314Z\314Z\314Z\314Z\314Z\314Z\314Zv\255\377\377"
  "\377\377\377\377\377\377\377\377\377\377\377\377v\255\314Z\314Z\314Z\314"
  "Z\314Z\314Z\314Z\314Z\314Z\314Z\314Z\314Z\314Z\314Z\314Z\314Z\314Z\314Z\314"
  "Z\314Z\314Z\314Z\071\306\377\377\377\377\377\377\377\377\377\377\377\377\377"
  "\377\071\306\314Z\314Z\314Z\314Z\314Z\314Z\314Z\314Z\314Z\314Z\314Z\314Z\314"
  "Z\314Z\314Z\314Z\314Z\314Z\314Z\314Z\314Z\314Z\333\336\377\377\377\377\377"
  "\377\377\377\377\377\377\377\377\377\333\336\314Z\314Z\314Z\314Z\314Z\314"
  "Z\314Z\314Z\314Z\314Z\314Z\314Z\314Z\314Z\314Z\314Z\314Z\314Z\314Z\314Z\314"
  "Z\314Z}\357\377\377\377\377\377\377\377\377\377\377\377\377\377\377}\357"
  "\314Z\314Z\314Z\314Z\314Z\314Z\314Z\314Z\314Z\314Z\314Z\314Z\314Z\314ZU\255"
  "\377\377<\347\226\265-c\314Z\354Z\327\275\377\377\377\377\377\377\377\377"
  "\377\377\377\377\377\377\377\377\377\377\367\275\354Z\314Z-c\226\265<\347"
  "\377\377U\255\314Z\314Z\314Z\314Z\314Znk\276\367\377\377\377\377\377\377"
  "\337\377\272\326}\357\377\377\377\377\377\377\377\377\377\377\377\377\377"
  "\377\377\377\377\377\377\377\377\377~\357\272\326\337\377\377\377\377\377"
  "\377\377\276\367nk\314Z\314Z\314Z\314Zy\316\377\377\377\377\377\377\377\377"
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
  "Z\354Z\327\275\377\377\377\377\377\377\377\377\377\377\377\377\377\377\377"
  "\377\377\377\327\275\354Z\314Z-c\226\265<\347\377\377U\255\314Z\314Z\314"
  "Z\314Z\314Z\314Z\314Z\314Z\314Z\314Z\314Z\314Z\314Z\314Z}\357\377\377\377"
  "\377\377\377\377\377\377\377\377\377\377\377}\357\314Z\314Z\314Z\314Z\314"
  "Z\314Z\314Z\314Z\314Z\314Z\314Z\314Z\314Z\314Z\314Z\314Z\314Z\314Z\314Z\314"
  "Z\314Z\314Z\333\336\377\377\377\377\377\377\377\377\377\377\377\377\377\377"
  "\333\336\314Z\314Z\314Z\314Z\314Z\314Z\314Z\314Z\314Z\314Z\314Z\314Z\314"
  "Z\314Z\314Z\314Z\314Z\314Z\314Z\314Z\314Z\314Z\071\306\377\377\377\377\377"
  "\377\377\377\377\377\377\377\377\377\071\306\314Z\314Z\314Z\314Z\314Z\314"
  "Z\314Z\314Z\314Z\314Z\314Z\314Z\314Z\314Z\314Z\314Z\314Z\314Z\314Z\314Z\314"
  "Z\314Zv\255\377\377\377\377\377\377\377\377\377\377\377\377\377\377v\255"
  "\314Z\314Z\314Z\314Z\314Z\314Z\314Z\314Z\314Z\314Z\314Z\314Z\314Z\314Z\314"
  "Z\314Z\314Z\314Z\314Z\314Z\314Z\314ZNk\373\336]\357]\357]\357]\357]\357\373"
  "\336Mk\314Z\314Z\314Z\314Z\314Z\314Z\314Z\314Z\314Z\314Z\314Z"

};

Image IMAGE_SETTINGS = {31, 31, (const uint16_t*)(data)};
