median-dispersion/GMT-Geiger-Counter/Firmware/GMT-Geiger-Counter/ImageDecrease.cpp

#include "Graphics.h"

const PROGMEM uint8_t data[] = {

  "\314Z\314Z\314Z\314Z\314Z\314Z\314Z\314Z\314Z\314Z\314Z\314Z\314Z\314Z\314"
  "ZMk\024\245\354Z\314Z\314Z\314Z\314Z\314Z\314Z\314Z\314Z\314Z\314Z\314Z\363"
  "\234\216s\314Z\314Z\314Z\314Z\314Z\314Z\314Z\314Z\314Z\314Z\314Z\314Z\314"
  "Z\314Z\226\265\276\367\377\377\327\275\314Z\314Z\314Z\314Z\314Z\314Z\314"
  "Z\314Z\314Z\263\224]\357\377\377\034\347\314Z\314Z\314Z\314Z\314Z\314Z\314"
  "Z\314Z\314Z\314Z\314Z\314Z\222\224<\347\377\377\377\377\377\377\071\306\314"
  "Z\314Z\314Z\314Z\314Z\314Z\314Z\257s\272\326\377\377\377\377\377\377]\357"
  "\314Z\314Z\314Z\314Z\314Z\314Z\314Z\314Z\314Z\314Z\317{\272\326\377\377\377"
  "\377\377\377\377\377\377\377\071\306\314Z\314Z\314Z\314Z\314Z\015c\367\275"
  "\337\377\377\377\377\377\377\377\377\377]\357\314Z\314Z\314Z\314Z\314Z\314"
  "Z\314Z\314Z\015c\367\275\337\377\377\377\377\377\377\377\377\377\377\377\377"
  "\377\071\306\314Z\314Z\314Z\314Z\024\245\236\367\377\377\377\377\377\377\377"
  "\377\377\377\377\377]\357\314Z\314Z\314Z\314Z\314Z\314Z\314Z\024\245\236\367"
  "\377\377\377\377\377\377\377\377\377\377\377\377\377\377\377\377\071\306\314"
  "Z\314Zr\214<\347\377\377\377\377\377\377\377\377\377\377\377\377\377\377"
  "\377\377]\357\314Z\314Z\314Z\314Z\314Zr\214<\347\377\377\377\377\377\377"
  "\377\377\377\377\377\377\377\377\377\377\377\377\377\377\071\306nky\316\377"
  "\377\377\377\377\377\377\377\377\377\377\377\377\377\377\377\377\377\377"
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
  "\314Z\314Z\314Z\314Z\314Z\314Z\314Z\314Z\314Z\314Z\314Z\314Z\314Z\314Z\314"
  "ZMk\364\234\314Z\314Z\314Z\314Z\314Z\314Z\314Z\314Z\314Z\314Z\314Z\314Z\323"
  "\234nk"

};

Image IMAGE_DECREASE = {31, 21, (const uint16_t*)(data)};
