median-dispersion/GMT-Geiger-Counter/Firmware/GMT-Geiger-Counter/ImageHotspot.cpp

#include "Graphics.h"

const PROGMEM uint8_t data[] = {

  "\314Z\314Z\314Z\314Z\314Z\314Z\314Z\314Z\314Z\314Z\015c\363\234\070\306\333"
  "\336<\347]\357<\347\333\336\070\306\363\234\354Z\314Z\314Z\314Z\314Z\314Z"
  "\314Z\314Z\314Z\314Z\314Z\314Z\314Z\314Z\314Z\314Z\314Z\314Z\314Z\257sy\316"
  "\337\377\377\377\377\377\377\377\377\377\377\377\377\377\377\377\377\377"
  "\377\377\276\367y\316\217s\314Z\314Z\314Z\314Z\314Z\314Z\314Z\314Z\314Z\314"
  "Z\314Z\314Z\314Z\314Z\015c\070\306\337\377\377\377\377\377\377\377\034\347y"
  "\316\370\275\226\265\370\275y\316\034\347\377\377\377\377\377\377\337\377"
  "\030\306\015c\314Z\314Z\314Z\314Z\314Z\314Z\314Z\314Z\314Z\314Z\314Z\257s]"
  "\357\377\377\377\377}\357\226\265nk\314Z\314Z\314Z\314Z\314Z\314Z\314Znk"
  "\226\265~\357\377\377\377\377]\357\257s\314Z\314Z\314Z\314Z\314Z\314Z\314"
  "Z\314Z\314Zr\214\276\367\377\377\337\377\267\265\354Z\314Z\314Z\314Z\314"
  "Z\314Z\314Z\314Z\314Z\314Z\314Z\314Z\354Z\267\265\337\377\377\377\236\367"
  "Q\214\314Z\314Z\314Z\314Z\314Z\314Z\314Z\257s\236\367\377\377\236\367r\214"
  "\314Z\314Z\314Z\314Z\314Z\314Z\314Z\314Z\314Z\314Z\314Z\314Z\314Z\314Z\314"
  "ZQ\214\236\367\377\377\276\367\317{\314Z\314Z\314Z\314Z\314Z\015c]\357\377"
  "\377\236\367\257s\314Z\314Z\314Z\314Z\314Z\314Z\015c\061\204\222\224\061\204"
  "\354Z\314Z\314Z\314Z\314Z\314Z\314Z\257s\236\367\377\377]\357\015c\314Z\314"
  "Z\314Z\314Z\070\306\377\377\337\377Q\214\314Z\314Z\314Z\314Z\314Z\263\224"
  "\373\336\337\377\377\377\377\377\377\377\337\377\373\336\263\224\314Z\314"
  "Z\314Z\314Z\314Zr\214\337\377\377\377\030\306\314Z\314Z\314Z\257s\337\377"
  "\377\377\267\265\314Z\314Z\314Z\314Z\015c\272\326\377\377\377\377\377\377"
  "\377\377\337\377\377\377\377\377\377\377\377\377\272\326\015c\314Z\314Z\314"
  "Z\314Z\327\275\377\377\337\377\216s\314Z\314Zy\316\377\377}\357\354Z\314"
  "Z\314Z\314Z\015c<\347\377\377\377\377\333\336\363\234\015c\314Z\015c\364\234"
  "\333\336\377\377\377\377<\347\015c\314Z\314Z\314Z\354Z\236\367\377\377y\316"
  "\314Z\015c\276\367\377\377\226\265\314Z\314Z\314Z\314Z\272\326\377\377\337"
  "\377\065\245\314Z\314Z\314Z\314Z\314Z\314Z\314Z\065\245\337\377\377\377\272"
  "\326\314Z\314Z\314Z\314Z\226\265\377\377\276\367\354Z\363\234\377\377\377"
  "\377nk\314Z\314Z\314Z\263\224\377\377\377\377\065\245\314Z\314Z\314Z\314Z"
  "\314Z\314Z\314Z\314Z\314ZU\255\377\377\377\377\263\224\314Z\314Z\314Znk\377"
  "\377\377\377\323\234\070\306\377\377\034\347\314Z\314Z\314Z\314Z\373\336\377"
  "\377\333\336\314Z\314Z\314Z\314Z\314Z\314Z\314Z\314Z\314Z\314Z\314Z\373\336"
  "\377\377\333\336\314Z\314Z\314Z\314Z\034\347\377\377\030\306\333\336\377\377"
  "y\316\314Z\314Z\314Z\015c\337\377\377\377\363\234\314Z\314Z\314Z\314Z\226"
  "\265\272\326\226\265\314Z\314Z\314Z\314Z\364\234\377\377\337\377\015c\314"
  "Z\314Z\314Zy\316\377\377\333\336<\347\377\377\370\275\314Z\314Z\314Z\020\204"
  "\377\377\377\377\015c\314Z\314Z\314Z\226\265\377\377\377\377\377\377\226\265"
  "\314Z\314Z\314Z-c\377\377\377\377\020\204\314Z\314Z\314Z\370\275\377\377<"
  "\347]\357\377\377\226\265\314Z\314Z\314Z\262\224\377\377\337\377\314Z\314"
  "Z\314Z\314Z\272\326\377\377\377\377\377\377\272\326\314Z\314Z\314Z\314Z\337"
  "\377\377\377\222\224\314Z\314Z\314Z\226\265\377\377]\357\373\336\377\377"
  "\370\275\314Z\314Z\314Z\020\204\377\377\377\377-c\314Z\314Z\314Z\226\265\377"
  "\377\377\377\377\377\226\265\314Z\314Z\314Z-c\377\377\377\377\020\204\314"
  "Z\314Z\314Z\370\275\377\377<\347\232\326\377\377y\316\314Z\314Z\314Z\354"
  "Z\337\377\377\377\024\245\314Z\314Z\314Z\314Z\226\265\272\326\226\265\314"
  "Z\314Z\314Z\314Z\024\245\377\377\337\377\354Z\314Z\314Z\314Zz\316\377\377"
  "\273\326\030\306\377\377<\347\314Z\314Z\314Z\314Z\333\336\377\377\373\336"
  "\314Z\314Z\314Z\314Z\314Z\314Z\314Z\314Z\314Z\314Z\314Z\374\336\377\377\333"
  "\336\314Z\314Z\314Z\314Z<\347\377\377\370\275r\214\377\377\377\377\216s\314"
  "Z\314Z\314Z\222\224\377\377\377\377u\255\314Z\314Z\314Z\314Z\314Z\314Z\314"
  "Z\314Z\314Zv\255\377\377\377\377\222\224\314Z\314Z\314Z\217s\377\377\377"
  "\377r\214\314Z\236\367\377\377\266\265\314Z\314Z\314Z\314Z\232\326\377\377"
  "\337\377\217s\314Z\314Z\314Z\314Z\314Z\314Z\314Z\257s\337\377\377\377\232"
  "\326\314Z\314Z\314Z\314Z\267\265\377\377\236\367\314Z\314ZY\316\377\377\236"
  "\367\015c\314Z\314Z\314Z\015c\034\347}\357-c\314Z\314Z\314Z\314Z\314Z\314Z\314"
  "ZMk}\357\034\347\015c\314Z\314Z\314Z\015c\236\367\377\377\071\306\314Z\314Zn"
  "k\337\377\377\377\367\275\314Z\314Z\314Z\314Z\314Z\314Z\314Z\314Z\314Z\314"
  "Z\314Z\314Z\314Z\314Z\314Z\314Z\314Z\314Z\314Z\314Z\314Z\370\275\377\377"
  "\337\377nk\314Z\314Z\314Z\370\275\377\377\377\377\323\234\314Z\314Z\314Z"
  "\314Z\314Z\314Z\314Z\314Z\314Z\314Z\314Z\314Z\314Z\314Z\314Z\314Z\314Z\314"
  "Z\314Z\263\224\337\377\377\377\367\275\314Z\314Z\314Z\314Z\354Z]\357\377"
  "\377\276\367\317{\314Z\314Z\314Z\314Z\314Z\314Z\314Z\314Z\314Z\314Z\314Z"
  "\314Z\314Z\314Z\314Z\314Z\314Z\317{\276\367\377\377]\357\354Z\314Z\314Z\314"
  "Z\314Z\314Z\360{\276\367\377\377\070\306\314Z\314Z\314Z\314Z\314Z\314Z\314"
  "Z\314Z\314Z\314Z\314Z\314Z\314Z\314Z\314Z\314Z\314Z\070\306\377\377\236\367"
  "\360{\314Z\314Z\314Z\314Z\314Z\314Z\314Z\061\204y\316\360{\314Z\314Z\314Z"
  "\314Z\314Z\314Z\314Z\314Z\314Z\314Z\314Z\314Z\314Z\314Z\314Z\314Z\314Z\360"
  "{y\316\061\204\314Z\314Z\314Z\314Z"

};

Image IMAGE_HOTSPOT = {31, 27, (const uint16_t*)(data)};
