median-dispersion/GMT-Geiger-Counter/Firmware/GMT-Geiger-Counter/ImageIncrease.cpp

#include "Graphics.h"

const PROGMEM uint8_t data[] = {

  "\216s\363\234\314Z\314Z\314Z\314Z\314Z\314Z\314Z\314Z\314Z\314Z\314Z\354"
  "Z\024\245Mk\314Z\314Z\314Z\314Z\314Z\314Z\314Z\314Z\314Z\314Z\314Z\314Z\314"
  "Z\314Z\314Z\034\347\377\377]\357\263\224\314Z\314Z\314Z\314Z\314Z\314Z\314"
  "Z\314Z\314Z\327\275\377\377\276\367\226\265\314Z\314Z\314Z\314Z\314Z\314"
  "Z\314Z\314Z\314Z\314Z\314Z\314Z\314Z\314Z]\357\377\377\377\377\377\377\373"
  "\336\360{\314Z\314Z\314Z\314Z\314Z\314Z\314Z\071\306\377\377\377\377\377\377"
  "]\357\263\224\314Z\314Z\314Z\314Z\314Z\314Z\314Z\314Z\314Z\314Z\314Z\314"
  "Z]\357\377\377\377\377\377\377\377\377\337\377\071\306-c\314Z\314Z\314Z\314"
  "Z\314Z\071\306\377\377\377\377\377\377\377\377\377\377\373\336\360{\314Z\314"
  "Z\314Z\314Z\314Z\314Z\314Z\314Z\314Z\314Z]\357\377\377\377\377\377\377\377"
  "\377\377\377\377\377\236\367v\255\314Z\314Z\314Z\314Z\071\306\377\377\377"
  "\377\377\377\377\377\377\377\377\377\337\377\071\306-c\314Z\314Z\314Z\314"
  "Z\314Z\314Z\314Z\314Z]\357\377\377\377\377\377\377\377\377\377\377\377\377"
  "\377\377\377\377=\347\222\224\314Z\314Z\071\306\377\377\377\377\377\377\377"
  "\377\377\377\377\377\377\377\377\377\236\367v\255\314Z\314Z\314Z\314Z\314"
  "Z\314Z\314Z]\357\377\377\377\377\377\377\377\377\377\377\377\377\377\377"
  "\377\377\377\377\377\377\272\326\257s\071\306\377\377\377\377\377\377\377"
  "\377\377\377\377\377\377\377\377\377\377\377\377\377]\357\222\224\314Z\314"
  "Z\314Z\314Z\314Z]\357\377\377\377\377\377\377\377\377\377\377\377\377\377"
  "\377\377\377\377\377\377\377\377\377\337\377]\357\377\377\377\377\377\377"
  "\377\377\377\377\377\377\377\377\377\377\377\377\377\377\377\377\377\377"
  "\232\326\257s\314Z\314Z\314Z]\357\377\377\377\377\377\377\377\377\377\377"
  "\377\377\377\377\377\377\377\377\377\377\377\377\377\377\377\377\377\377"
  "\377\377\377\377\377\377\377\377\377\377\377\377\377\377\377\377\377\377"
  "\377\377\377\377\377\377\337\377\030\306\015c\314Z]\357\377\377\377\377\377"
  "\377\377\377\377\377\377\377\377\377\377\377\377\377\377\377\377\377\377"
  "\377\377\377\377\377\377\377\377\377\377\377\377\377\377\377\377\377\377"
  "\377\377\377\377\377\377\377\377\377\377\377\377\377\377\377~\357\263\224"
  "]\357\377\377\377\377\377\377\377\377\377\377\377\377\377\377\377\377\377"
  "\377\377\377\377\377\377\377\377\377\377\377\377\377\377\377\377\377\377"
  "\377\377\377\377\377\377\377\377\377\377\377\377\377\377\377\377\377\377"
  "\377\377\377\377\377\034\347]\357\377\377\377\377\377\377\377\377\377\377"
  "\377\377\377\377\377\377\377\377\377\377\377\377\377\377\377\377\377\377"
  "\377\377\377\377\377\377\377\377\377\377\377\377\377\377\377\377\377\377"
  "\377\377\377\377\377\377\377\377\377\377~\357\263\224]\357\377\377\377\377"
  "\377\377\377\377\377\377\377\377\377\377\377\377\377\377\377\377\377\377"
  "\377\377\377\377\377\377\377\377\377\377\377\377\377\377\377\377\377\377"
  "\377\377\377\377\377\377\377\377\377\377\377\377\337\377\030\306\015c\314Z"
  "]\357\377\377\377\377\377\377\377\377\377\377\377\377\377\377\377\377\377"
  "\377\377\377\377\377\337\377]\357\377\377\377\377\377\377\377\377\377\377"
  "\377\377\377\377\377\377\377\377\377\377\377\377\377\377\232\326\257s\314"
  "Z\314Z\314Z]\357\377\377\377\377\377\377\377\377\377\377\377\377\377\377"
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
  "Z\314Z\314Znk\323\234\314Z\314Z\314Z\314Z\314Z\314Z\314Z\314Z\314Z\314Z\314"
  "Z\314Z\364\234Mk\314Z\314Z\314Z\314Z\314Z\314Z\314Z\314Z\314Z\314Z\314Z\314"
  "Z\314Z\314Z\314Z"

};

Image IMAGE_INCREASE = {31, 21, (const uint16_t*)(data)};
