median-dispersion/GMT-Geiger-Counter/Firmware/GMT-Geiger-Counter/ImagePower.cpp

#include "Graphics.h"

const PROGMEM uint8_t data[] = {

  "@\071@\071@\071@\071@\071@\071@\071@\071@\071@\071@\071\322\234\377\377\322\234@\071"
  "@\071@\071@\071@\071@\071@\071@\071@\071@\071@\071@\071@\071@\071@\071@\071@\071@\071@\071"
  "@\071@\071@\071\266\275\377\377\266\275@\071@\071@\071@\071@\071@\071@\071@\071@\071"
  "@\071@\071@\071@\071@\071@\071@\071@\071@\071\006J\363\244hR@\071\266\275\377\377\266"
  "\275@\071\211Z\363\244\006J@\071@\071@\071@\071@\071@\071@\071@\071@\071@\071@\071@\071"
  "A\071\225\265\276\367\377\377\027\306@\071\266\275\377\377\266\275@\071\030\306"
  "\377\377\276\367\225\265A\071@\071@\071@\071@\071@\071@\071@\071@\071@\071\210Z\034"
  "\347\377\377\377\377\333\336Lk@\071\266\275\377\377\266\275@\071Lk\333\336"
  "\377\377\377\377\373\346hR@\071@\071@\071@\071@\071@\071@\071\251Z]\357\377\377"
  "}\357\060\214@\071@\071@\071\266\275\377\377\266\275@\071@\071@\071\060\214}\357"
  "\377\377]\357\211Z@\071@\071@\071@\071@\071b\071\373\336\377\377\034\347hR@\071@"
  "\071@\071@\071\266\275\377\377\266\275@\071@\071@\071@\071hR<\347\377\377\373\336"
  "b\071@\071@\071@\071@\071\225\265\377\377}\357hR@\071@\071@\071@\071@\071\266\275\377"
  "\377\266\275@\071@\071@\071@\071@\071hR}\357\377\377u\265@\071@\071@\071'J\276\367"
  "\377\377\060\214@\071@\071@\071@\071@\071@\071\266\275\377\377\266\275@\071@\071@"
  "\071@\071@\071@\071\060\214\377\377\276\367\006J@\071@\071T\255\377\377\333\336@\071"
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
  "\377\377\276\367\272\336\064\245\006J@\071@\071@\071@\071@\071@\071@\071@\071@\071@\071"
  "@\071@\071@\071@\071@\071@\071@\071@\071\304A\352b\304A@\071@\071@\071@\071@\071@\071@"
  "\071@\071@\071@\071@\071"

};

Image IMAGE_POWER = {25, 26, (const uint16_t*)(data)};
