median-dispersion/GMT-Geiger-Counter/Firmware/GMT-Geiger-Counter/ImageReset.cpp

#include "Graphics.h"

const PROGMEM uint8_t data[] = {

  "\314Z\314Z\314Z\314Z\314Z\314Z\314Z\314Z\314Z\314Z\314Z\314ZQ\214\034\347"
  "\367\275\354Z\314Z\314Z\314Z\314Z\314Z\314Z\314Z\314Z\314Z\314Z\314Z\314"
  "Z\314Z\314Z\314Z\314Z\314Z\314Z\314Z\314Z\314Z\030\306\377\377\377\377~\357"
  "\024\245\314Z\314Z\314Z\314Z\314Z\314Z\314Z\314Z\314Z\314Z\314Z\314Z\314Z"
  "\314Z\314Z\314Z\314Z\314Z\314Z\314Z\030\306\377\377\377\377\377\377\377\377"
  "\034\347Q\214\314Z\314Z\314Z\314Z\314Z\314Z\314Z\314Z\314Z\314Z\314Z\314Z"
  "\314Z\314Z\314Z\317{\065\245\327\275\034\347\377\377\377\377\377\377\377\377"
  "\377\377\377\377y\316\354Z\314Z\314Z\314Z\314Z\314Z\314Z\314Z\314Z\314Z\314"
  "Z\354Z\266\265]\357\377\377\377\377\377\377\377\377\377\377\377\377\377\377"
  "\377\377\377\377\377\377\377\377\024\245\314Z\314Z\314Z\314Z\314Z\314Z\314"
  "Z\314Z\314Z\323\234}\357\377\377\377\377\377\377\236\367<\347}\357\377\377"
  "\377\377\377\377\377\377\377\377\377\377\373\336-c\314Z\314Z\314Z\314Z\314"
  "Z\314Z\314Z\314Z\267\265\377\377\377\377\337\377\071\306\061\204\314Z\314Z"
  "\030\306\377\377\377\377\377\377\377\377}\357\363\234\314Z\314Z\314Z\314Z"
  "\314Z\314Z\314Z\314Z\314Z\267\265\377\377\377\377\374\336\257s\314Z\314Z"
  "\314Z\314Z\030\306\377\377\377\377\276\367\267\265\314Z\314Z\314Z\314Z\314"
  "Z\314Z\314Z\314Z\314Z\314Z\323\234\377\377\377\377\232\326\314Z\314Z\314"
  "Z\314Z\314Z\314Z\222\224\236\367y\316nk\314Z\314Z\314Z\314Z\314Z\314Z\314"
  "Z\314Z\314Z\314Z\314Z}\357\377\377\034\347\314Z\314Z\314Z\314Z\314Z\314Z\314"
  "Z\314Z\314Z\314Z\314Z\314Z\314Z\314Z\314Z\314Z\314Z\314Z\314Z\314Z\314Z\266"
  "\265\377\377\337\377\257s\314Z\314Z\314Z\314Z\314Z\314Z\314Z\314Z\314Z\314"
  "Z\314Z\314Z\314Z\314Z\314Z\314Z\314Z\314Z\314Z\314Z\314Z]\357\377\377\071"
  "\306\314Z\314Z\314Z\314Z\314Z\314Z\314Z\363\234]\357\363\234\314Z\314Z\314"
  "Z\314Z\314Z\314Z\314Z\314Z\314Z\314Z\314Z\257s\377\377\377\377\061\204\314"
  "Z\314Z\314Z\314Z\314Z\314Z\314Z}\357\377\377}\357\314Z\314Z\314Z\314Z\314"
  "Z\314Z\314Z\314Z\314Z\314Z\314Z\065\245\377\377\236\367\314Z\314Z\314Z\314"
  "Z\314Z\314Z\314Zu\255\377\377\377\377\377\377u\255\314Z\314Z\314Z\314Z\314"
  "Z\314Z\314Z\314Z\314Z\314Z\327\275\377\377\034\347\314Z\314Z\314Z\314Z\314"
  "Z\314Z\314Z}\357\377\377\337\377\377\377}\357\314Z\314Z\314Z\314Z\314Z\314"
  "Z\314Z\061\204Y\316\257s\070\306\377\377\333\336\314Z\314Z\314Z\314Z\314Z\314"
  "Zu\255\377\377\337\377\222\224\337\377\377\377u\255\314Z\314Z\314Z\314Z\314"
  "Z\314Z\272\326\377\377\030\306\327\275\377\377\034\347\314Z\314Z\314Z\314Z"
  "\314Z\314Z}\357\377\377\377\377\276\367\377\377\377\377}\357\314Z\314Z\314"
  "Z\314Z\314Z\314Z<\347\377\377\267\265\065\245\377\377\236\367\314Z\314Z\314"
  "Z\314Z\314Zu\255\377\377\377\377\377\377\377\377\377\377\377\377\377\377"
  "u\255\314Z\314Z\314Z\314Z\314Z\236\367\377\377\065\245\317{\377\377\377\377"
  "\061\204\314Z\314Z\314Z\314Z]\357\377\377\272\326\363\234\363\234\363\234"
  "\272\326\377\377<\347\314Z\314Z\314Z\314ZQ\214\377\377\377\377\257s\314Z"
  "]\357\377\377\071\306\314Z\314Z\314Z\314Z\030\306<\347\257s\314Z\314Z\314Z"
  "\257s<\347\030\306\314Z\314Z\314Z\314ZY\316\377\377]\357\314Z\314Z\266\265"
  "\377\377\337\377\257s\314Z\314Z\314Z\314Z\314Z\314Z\314Z\314Z\314Z\314Z\314"
  "Z\314Z\314Z\314Z\314Z\257s\337\377\377\377\226\265\314Z\314Z\314Z}\357\377"
  "\377\034\347\314Z\314Z\314Z\314Z\314Z\314Z\314Z\314Z\314Z\314Z\314Z\314Z\314"
  "Z\314Z\314Z\373\336\377\377}\357\314Z\314Z\314Z\314Z\323\234\377\377\377"
  "\377\232\326\314Z\314Z\314Z\314Z\314Z\314Z\314Z\314Z\314Z\314Z\314Z\314Z"
  "\314Z\232\326\377\377\377\377\323\234\314Z\314Z\314Z\314Z\314Z\267\265\377"
  "\377\377\377\034\347\257s\314Z\314Z\314Z\314Z\314Z\314Z\314Z\314Z\314Z\257"
  "s\034\347\377\377\377\377\266\265\314Z\314Z\314Z\314Z\314Z\314Z\314Z\267\265"
  "\377\377\377\377\337\377\071\306Q\214\314Z\314Z\314Z\314Z\314ZQ\214Y\316\337"
  "\377\377\377\377\377\266\265\314Z\314Z\314Z\314Z\314Z\314Z\314Z\314Z\314"
  "Z\323\234}\357\377\377\377\377\377\377\236\367<\347\333\336<\347\236\367"
  "\377\377\377\377\377\377}\357\323\234\314Z\314Z\314Z\314Z\314Z\314Z\314Z"
  "\314Z\314Z\314Z\314Z\314Z\266\265]\357\377\377\377\377\377\377\377\377\377"
  "\377\377\377\377\377]\357\226\265\314Z\314Z\314Z\314Z\314Z\314Z\314Z\314"
  "Z\314Z\314Z\314Z\314Z\314Z\314Z\314Z\314Z\257s\065\245\327\275\070\306\327"
  "\275\065\245\257s\314Z\314Z\314Z\314Z\314Z\314Z\314Z\314Z\314Z"

};

Image IMAGE_RESET = {25, 28, (const uint16_t*)(data)};
