median-dispersion/GMT-Geiger-Counter/Firmware/GMT-Geiger-Counter/ImageResetSystem.cpp

#include "Graphics.h"

const PROGMEM uint8_t data[] = {

  "\000\060\000\060\000\060\000\060\000\060\000\060\000\060\000\060\000\060\000\060\000\060\363\244\377\377y"
  "\316\212Z\000\060\000\060\000\060\000\060\000\060\000\060\000\060\000\060\000\060\000\060\000\060\000\060\000\060"
  "\000\060\000\060\000\060\000\060\000\060\000\060\327\275\377\377\377\377\337\377\327\275EA"
  "\000\060\000\060\000\060\000\060\000\060\000\060\000\060\000\060\000\060\000\060\000\060\000\060\000\060\000\060\000"
  "\060\000\060\307I\070\316\377\377\377\377\377\377\377\377}\357\262\234\000\060\000"
  "\060\000\060\000\060\000\060\000\060\000\060\000\060\000\060\000\060\000\060\303\060\363\244\272\326\337"
  "\377\377\377\377\377\377\377\377\377\377\377\377\377\377\377\377\377\363"
  "\244\000\060\000\060\000\060\000\060\000\060\000\060\000\060\000\060\000\060q\224]\357\377\377\377\377"
  "\377\377\236\367\236\367\377\377\377\377\377\377\377\377\377\377\236\367"
  "\216s\000\060\000\060\000\060\000\060\000\060\000\060\000\060\000\060\266\275\377\377\377\377<\347"
  "\363\244\307I\000\060\327\275\377\377\377\377\377\377\337\377\367\275\246A\000"
  "\060\000\060\000\060\000\060\000\060\000\060\000\060\000\060\266\275\377\377\337\377\064\245\000\060"
  "\000\060\000\060\000\060\327\275\377\377\377\377\272\326\353j\000\060\000\060\000\060\000\060"
  "\000\060\000\060\000\060\000\060\000\060q\224\377\377\337\377\020\214\000\060\000\060\000\060\000\060"
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
  "\060\000\060\000\060\000\060\000\060\000\060\000\060\000\060\000\060\000\060\000\060\000\060\307I\014k\307I"
  "\000\060\000\060\000\060\000\060\000\060\000\060\000\060\000\060\000\060\000\060"

};

Image IMAGE_RESET_SYSTEM = {23, 25, (const uint16_t*)(data)};
