median-dispersion/GMT-Geiger-Counter/Firmware/GMT-Geiger-Counter/ImageSleep.cpp

#include "Graphics.h"

const PROGMEM uint8_t data[] = {

  "\314Z\314Z\314Z\314Z\314Z\314Z\314Z\314Z\314Z\314Z\314Z\314Z\314Z\314Z\314"
  "Z\314Z\314Z\314Z\314Z\314Z\314Z\314Znk\323\234\363\234\363\234\363\234\363"
  "\234\363\234\323\234\015c\314Z\314Z\314Z\314Z\314Z\314Z\314Z\314Z\314Z\314"
  "Z\314Z\314Z\314Z\314Z\314Z\314Z\314Z\314Z\314Z\314Z\314Z\314Z\314Z\314Z\314"
  "Z]\357\377\377\377\377\377\377\377\377\377\377\377\377\377\377\333\336\314"
  "Z\314Z\314Z\314Z\314Z\314Z\314Z\314Z\314Z\314Z\314Z\314Z\314Z\314Z\314Z\314"
  "Z\314Z\314Z\314Z\314Z\314Z\314Z\314Z\314Z\314Z\232\326\276\367\276\367\276"
  "\367\276\367\377\377\377\377\377\377\070\306\314Z\314Z\314Z\314Z\314Z\314"
  "Z\314Z\314Z\314Z\314Z\314Z\314Z\314Z\314Z\314Z\314Z\314Z\314Z\314Z\314Z\314"
  "Z\314Z\314Z\314Z\314Z\314Z\314Z\314Z\314Z\367\275\377\377\377\377\232\326"
  "\314Z\314Z\314Z\314Z\314Z\314Z\314Z\314Z\314Z\314Z\314Z\314Z\314Z\314Z\314"
  "Z\314Z\314Z\314Z\314Z\314Z\314Z\314Z\314Z\314Z\314Z\314Z\314Z\314Z\314Z\367"
  "\275\377\377\377\377\232\326\314Z\314Z\314Z\314Z\314Z\314Z\314Z\314Z\314"
  "Z\314Z\314Z\314Z\314Z\314Z\314Z\314Z\030\306\236\367\236\367\236\367\236\367"
  "\236\367\236\367\236\367\370\275\314Z\314Z\314Z\314Z\030\306\377\377\377\377"
  "\232\326\314Z\314Z\314Z\314Z\314Z\314Z\314Z\314Z\314Z\314Z\314Z\314Z\314"
  "Z\314Z\314Z\314Z\314Z<\347\377\377\377\377\377\377\377\377\377\377\377\377"
  "\377\377<\347\314Z\314Z\314Z\030\306\377\377\377\377\232\326\314Z\314Z\314"
  "Z\314Z\314Z\314Z\314Z\314Z\314Z\314Z\314Z\314Z\314Z\314Z\314Z\314Z\314Z\314"
  "Z\217s\065\245U\255U\255\030\306\377\377\377\377\236\367\020\204\314Z\314Z\367"
  "\275\377\377\377\377\377\377\333\336\333\336\333\336\333\336\024\245\314Z"
  "\314Z\314Z\314Z\314Z\314Z\314Z\314Z\314Z\314Z\314Z\314Z\314Z\314Z\314Z\314"
  "Z\314Z\020\204\236\367\377\377\236\367\020\204\314Z\314Z\314Z\236\367\377\377"
  "\377\377\377\377\377\377\377\377\377\377\377\377\034\347\314Z\314Z\314ZQ\214"
  "\367\275\367\275\367\275\367\275\367\275\367\275\367\275\222\224\314Z\314"
  "Z\314Z\314Z\020\204\236\367\377\377\236\367\020\204\314Z\314Z\314Z\314Z\222"
  "\224\070\306\071\306\071\306\071\306\071\306\071\306\070\306Q\214\314Z\314Z\314"
  "Z<\347\377\377\377\377\377\377\377\377\377\377\377\377\377\377\236\367\314"
  "Z\314Z\314Z\020\204\236\367\377\377\236\367\020\204\314Z\314Z\314Z\314Z\314"
  "Z\314Z\314Z\314Z\314Z\314Z\314Z\314Z\314Z\314Z\314Z\314Z\314Z\024\245\333"
  "\336\333\336\333\336\333\336\377\377\377\377\377\377\367\275\314Z\314Z\020"
  "\204\236\367\377\377\377\377\030\306U\255U\255\065\245\217s\314Z\314Z\314Z"
  "\314Z\314Z\314Z\314Z\314Z\314Z\314Z\314Z\314Z\314Z\314Z\314Z\314Z\314Z\314"
  "Z\232\326\377\377\377\377\030\306\314Z\314Z\314Z<\347\377\377\377\377\377"
  "\377\377\377\377\377\377\377\377\377<\347\314Z\314Z\314Z\314Z\314Z\314Z\314"
  "Z\314Z\314Z\314Z\314Z\314Z\314Z\314Z\314Z\314Z\314Z\232\326\377\377\377\377"
  "\030\306\314Z\314Z\314Z\314Z\370\275\236\367\236\367\236\367\236\367\236\367"
  "\236\367\236\367\030\306\314Z\314Z\314Z\314Z\314Z\314Z\314Z\314Z\314Z\314"
  "Z\314Z\314Z\314Z\314Z\314Z\314Zz\316\377\377\377\377\030\306\314Z\314Z\314"
  "Z\314Z\314Z\314Z\314Z\314Z\314Z\314Z\314Z\314Z\314Z\314Z\314Z\314Z\314Z\314"
  "Z\314Z\314Z\314Z\314Z\314Z\314Z\314Z\314Z\314Z\314Z\314Zz\316\377\377\377"
  "\377\030\306\314Z\314Z\314Z\314Z\314Z\314Z\314Z\314Z\314Z\314Z\314Z\314Z\314"
  "Z\314Z\314Z\314Z\314Z\314Z\314Z\314Z\314Z\314Z\314Z\314Z\314Z\314Z\314Z\314"
  "Z\314Z\070\306\377\377\377\377\377\377\276\367\276\367\276\367\276\367\232"
  "\326\314Z\314Z\314Z\314Z\314Z\314Z\314Z\314Z\314Z\314Z\314Z\314Z\314Z\314"
  "Z\314Z\314Z\314Z\314Z\314Z\314Z\314Z\314Z\314Z\314Z\314Z\333\336\377\377"
  "\377\377\377\377\377\377\377\377\377\377\377\377]\357\314Z\314Z\314Z\314"
  "Z\314Z\314Z\314Z\314Z\314Z\314Z\314Z\314Z\314Z\314Z\314Z\314Z\314Z\314Z\314"
  "Z\314Z\314Z\314Z\314Z\314Z\314Z\015c\323\234\363\234\363\234\363\234\363\234"
  "\363\234\323\234nk\314Z\314Z\314Z\314Z\314Z\314Z\314Z\314Z\314Z\314Z\314"
  "Z\314Z\314Z\314Z\314Z\314Z\314Z\314Z\314Z\314Z\314Z\314Z\314Z\314Z\314Z"

};

Image IMAGE_SLEEP = {34, 19, (const uint16_t*)(data)};
