median-dispersion/GMT-Geiger-Counter/Firmware/GMT-Geiger-Counter/ImageVolume.cpp

#include "Graphics.h"

const PROGMEM uint8_t data[] = {

  "\314Z\314Z\314Z\314Z\314Z\314Z\314Z\314Z\314Z\314Z\015c\364\234\015c\314Z\314"
  "Z\314Z\314Z\314Z\314Z\314Z\314Z\314Z\314Z\314Z\314Z\314Z\314Z\314Z\314Z\314"
  "Z\314Z\314Z\020\204]\357\377\377\070\306\314Z\314ZY\316\070\306nk\314Z\314Z"
  "\314Z\314Z\314Z\314Z\314Z\314Z\314Z\314Z\314Z\314Z\314Z\024\245\337\377\377"
  "\377\377\377z\316\314Z\061\204\377\377\377\377\337\377U\255\314Z\314Z\314"
  "Z\314Z\314Z\314Z\314Z\314Z\314Z\314Z\314Z\071\306\377\377\377\377\377\377"
  "\377\377z\316\314Z\314Z\226\265\236\367\377\377\377\377\370\275\314Z\314"
  "Z\314Z-c\370\275\071\306\071\306\071\306\071\306\034\347\377\377\377\377\377\377"
  "\377\377\377\377z\316\314Z\314Z\314Z-c\272\326\377\377\377\377v\255\314Z"
  "\314Z\226\265\377\377\377\377\377\377\377\377\377\377\377\377\377\377\377"
  "\377\377\377\377\377\377\377z\316\314Z\314Z\314Z\314Z\314Z\272\326\377\377"
  "\337\377\257s\314Z\327\275\377\377\377\377\377\377\377\377\377\377\377\377"
  "\377\377\377\377\377\377\377\377\377\377z\316\314Z\314Zu\255\262\224\314"
  "Z\015c\236\367\377\377Y\316\314Z\327\275\377\377\377\377\377\377\377\377\377"
  "\377\377\377\377\377\377\377\377\377\377\377\377\377z\316\314ZQ\214\377\377"
  "\337\377\061\204\314Z\226\265\377\377\276\367\314Z\327\275\377\377\377\377"
  "\377\377\377\377\377\377\377\377\377\377\377\377\377\377\377\377\377\377"
  "z\316\314Z\222\224\377\377\377\377\273\326\314Z-c\377\377\377\377r\214\327"
  "\275\377\377\377\377\377\377\377\377\377\377\377\377\377\377\377\377\377"
  "\377\377\377\377\377z\316\314Z\222\224\377\377\377\377\337\377\314Z\314Z"
  "}\357\377\377u\255\327\275\377\377\377\377\377\377\377\377\377\377\377\377"
  "\377\377\377\377\377\377\377\377\377\377z\316\314Z\222\224\377\377\377\377"
  "\377\377\015c\314Z<\347\377\377\267\265\327\275\377\377\377\377\377\377\377"
  "\377\377\377\377\377\377\377\377\377\377\377\377\377\377\377z\316\314Z\222"
  "\224\377\377\377\377\337\377\314Z\314Z}\357\377\377u\255\327\275\377\377"
  "\377\377\377\377\377\377\377\377\377\377\377\377\377\377\377\377\377\377"
  "\377\377z\316\314Z\222\224\377\377\377\377\273\326\314ZMk\377\377\377\377"
  "r\214\327\275\377\377\377\377\377\377\377\377\377\377\377\377\377\377\377"
  "\377\377\377\377\377\377\377z\316\314Z\061\204\377\377\337\377\061\204\314"
  "Z\226\265\377\377\276\367\314Z\327\275\377\377\377\377\377\377\377\377\377"
  "\377\377\377\377\377\377\377\377\377\377\377\377\377z\316\314Z\314Z\065\245"
  "\222\224\314Z\015c\236\367\377\377Y\316\314Z\226\265\377\377\377\377\377\377"
  "\377\377\377\377\377\377\377\377\377\377\377\377\377\377\377\377z\316\314"
  "Z\314Z\314Z\314Z\314Z\333\336\377\377\337\377\216s\314Z\015c\367\275\071\306"
  "\071\306\071\306\071\306\034\347\377\377\377\377\377\377\377\377\377\377z\316"
  "\314Z\314Z\314ZNk\333\336\377\377\377\377U\255\314Z\314Z\314Z\314Z\314Z\314"
  "Z\314Z\314Z\314Z\071\306\377\377\377\377\377\377\377\377z\316\314Z\314Z\267"
  "\265\276\367\377\377\377\377\327\275\314Z\314Z\314Z\314Z\314Z\314Z\314Z\314"
  "Z\314Z\314Z\314Z\024\245\337\377\377\377\377\377z\316\314Z\061\204\377\377"
  "\377\377\276\367\065\245\314Z\314Z\314Z\314Z\314Z\314Z\314Z\314Z\314Z\314"
  "Z\314Z\314Z\314Z\020\204]\357\377\377\030\306\314Z\314ZY\316\030\306Nk\314Z"
  "\314Z\314Z\314Z\314Z\314Z\314Z\314Z\314Z\314Z\314Z\314Z\314Z\314Z\314Z\015"
  "c\364\234\354Z\314Z\314Z\314Z\314Z\314Z\314Z\314Z\314Z\314Z\314Z"

};

Image IMAGE_VOLUME = {23, 21, (const uint16_t*)(data)};
