median-dispersion/GMT-Geiger-Counter/Firmware/GMT-Geiger-Counter/ImageWiFi.cpp

#include "Graphics.h"

const PROGMEM uint8_t data[] = {

  "\314Z\314Z\314Z\314Z\314Z\314Z\314Z\314Z\314Z\314Z\314Z\360{\024\245\327\275"
  "\030\306\071\306\030\306\327\275\024\245\360{\314Z\314Z\314Z\314Z\314Z\314Z\314"
  "Z\314Z\314Z\314Z\314Z\314Z\314Z\314Z\314Z\314Z\314Z\314Z\314Z\262\224\232"
  "\326\236\367\377\377\377\377\377\377\377\377\377\377\377\377\377\377\377"
  "\377\377\377\236\367z\316\222\224\314Z\314Z\314Z\314Z\314Z\314Z\314Z\314"
  "Z\314Z\314Z\314Z\314Z\314Z\314Z\065\245]\357\377\377\377\377\377\377\377\377"
  "\276\367<\347\333\336\333\336\333\336<\347\276\367\377\377\377\377\377\377"
  "\377\377]\357\065\245\314Z\314Z\314Z\314Z\314Z\314Z\314Z\314Z\314Z\314Z\061"
  "\204<\347\377\377\377\377\377\377\034\347\226\265\360{\314Z\314Z\314Z\314"
  "Z\314Z\314Z\314Z\360{\226\265\034\347\377\377\377\377\377\377<\347\061\204"
  "\314Z\314Z\314Z\314Z\314Z\314Z\314Z\226\265\337\377\377\377\377\377\232\326"
  "\020\204\314Z\314Z\314Z\314Z\314Z\314Z\314Z\314Z\314Z\314Z\314Z\314Z\314Z"
  "\020\204\232\326\377\377\377\377\337\377\226\265\314Z\314Z\314Z\314Z\314Z"
  "y\316\377\377\377\377]\357r\214\314Z\314Z\314Z\314Z\314Z\314Z\314Z\314Z\314"
  "Z\314Z\314Z\314Z\314Z\314Z\314Z\314Z\314Zr\214]\357\377\377\377\377y\316"
  "\314Z\314Z\314Zz\316\377\377\377\377\232\326\354Z\314Z\314Z\314Z\314Z\314"
  "Z\314Z\314Z\314Z\314Z\314Z\314Z\314Z\314Z\314Z\314Z\314Z\314Z\314Z\314Z\354"
  "Z\232\326\377\377\377\377z\316\314Z\363\234\377\377\377\377z\316\314Z\314"
  "Z\314Z\314Z\314Z\314Z\314Z\314Z\314Z\314Z\314Z\314Z\314Z\314Z\314Z\314Z\314"
  "Z\314Z\314Z\314Z\314Z\314Z\314Zz\316\377\377\377\377\363\234\216s\236\367"
  "\377\377\276\367Q\214\314Z\314Z\314Z\314Z\314Z\314Z\314Z\314Z\314Z\314Z\314"
  "Z\314Z\314Z\314Z\314Z\314Z\314Z\314Z\314Z\314Z\314ZQ\214\276\367\377\377"
  "\236\367nk\314Z\360{\236\367\377\377\276\367Q\214\314Z\314Z\314Z\314Z\314"
  "Z-c\065\245z\316\373\336<\347\373\336z\316\065\245-c\314Z\314Z\314Z\314Z\314"
  "ZQ\214\276\367\377\377\236\367\360{\314Z\314Z\314Z\317{\236\367\377\377\276"
  "\367Q\214\314Z\314Z-c\367\275\337\377\377\377\377\377\377\377\377\377\377"
  "\377\377\377\377\377\337\377\071\306Nk\314Z\314Z\061\204\276\367\377\377\236"
  "\367\360{\314Z\314Z\314Z\314Z\314Z\317{\236\367\377\377\276\367Q\214Q\214"
  "\236\367\377\377\377\377\377\377\377\377\377\377\377\377\377\377\377\377"
  "\377\377\377\377\377\377\236\367\222\224\061\204\276\367\377\377\236\367\360"
  "{\314Z\314Z\314Z\314Z\314Z\314Z\314Z\360{\236\367\377\377\276\367\337\377"
  "\377\377\377\377\377\377\377\377\377\377\377\377\377\377\377\377\377\377"
  "\377\377\377\377\377\377\377\377\337\377\276\367\377\377\236\367\360{\314"
  "Z\314Z\314Z\314Z\314Z\314Z\314Z\314Z\314Z\317{\236\367\377\377\377\377\377"
  "\377\377\377\377\377\377\377\377\377\377\377\377\377\377\377\377\377\377"
  "\377\377\377\377\377\377\377\377\377\377\377\236\367\360{\314Z\314Z\314Z"
  "\314Z\314Z\314Z\314Z\314Z\314Z\314Z\314Z\317{\236\367\377\377\377\377\377"
  "\377\377\377\377\377\377\377\377\377\377\377\377\377\377\377\377\377\377"
  "\377\377\377\377\377\377\377\236\367\360{\314Z\314Z\314Z\314Z\314Z\314Z\314"
  "Z\314Z\314Z\314Z\314Z\314Z\314Z\317{\236\367\377\377\377\377\377\377\377"
  "\377\377\377\377\377\377\377\377\377\377\377\377\377\377\377\377\377\377"
  "\377\236\367\360{\314Z\314Z\314Z\314Z\314Z\314Z\314Z\314Z\314Z\314Z\314Z"
  "\314Z\314Z\314Z\314Z\317{\236\367\377\377\377\377\377\377\377\377\377\377"
  "\377\377\377\377\377\377\377\377\377\377\377\377\236\367\360{\314Z\314Z\314"
  "Z\314Z\314Z\314Z\314Z\314Z\314Z\314Z\314Z\314Z\314Z\314Z\314Z\314Z\314Z\317"
  "{\236\367\377\377\377\377\377\377\377\377\377\377\377\377\377\377\377\377"
  "\377\377\236\367\360{\314Z\314Z\314Z\314Z\314Z\314Z\314Z\314Z\314Z\314Z\314"
  "Z\314Z\314Z\314Z\314Z\314Z\314Z\314Z\314Z\317{\236\367\377\377\377\377\377"
  "\377\377\377\377\377\377\377\377\377\236\367\360{\314Z\314Z\314Z\314Z\314"
  "Z\314Z\314Z\314Z\314Z\314Z\314Z\314Z\314Z\314Z\314Z\314Z\314Z\314Z\314Z\314"
  "Z\314Z\317{\236\367\377\377\377\377\377\377\377\377\377\377\236\367\360{"
  "\314Z\314Z\314Z\314Z\314Z\314Z\314Z\314Z\314Z\314Z\314Z\314Z\314Z\314Z\314"
  "Z\314Z\314Z\314Z\314Z\314Z\314Z\314Z\314Z\317{\236\367\377\377\377\377\377"
  "\377\236\367\360{\314Z\314Z\314Z\314Z\314Z\314Z\314Z\314Z\314Z\314Z\314Z"
  "\314Z\314Z\314Z\314Z\314Z\314Z\314Z\314Z\314Z\314Z\314Z\314Z\314Z\314Z\317"
  "{\236\367\377\377\236\367\360{\314Z\314Z\314Z\314Z\314Z\314Z\314Z\314Z\314"
  "Z\314Z\314Z\314Z\314Z\314Z\314Z\314Z\314Z\314Z\314Z\314Z\314Z\314Z\314Z\314"
  "Z\314Z\314Z\314Z\317{\030\306\317{\314Z\314Z\314Z\314Z\314Z\314Z\314Z\314"
  "Z\314Z\314Z\314Z\314Z\314Z\314Z"

};

Image IMAGE_WIFI = {31, 23, (const uint16_t*)(data)};
