median-dispersion/GMT-Geiger-Counter/Firmware/GMT-Geiger-Counter/ImageQuestion.cpp

#include "Graphics.h"

const PROGMEM uint8_t data[] = {

  "F)F)F)F)F)F)F)F)F)F)F)F)F)F)\247\061\257s\323\234U\255U\255U\255\323\234\216"
  "s\207\061F)F)F)F)F)F)F)F)F)F)F)F)F)F)F)F)F)F)F)F)F)F)F)F)F)jJU\255\373\336"
  "\337\377\377\377\377\377\377\377\377\377\377\377\377\377\377\377\337\377"
  "\333\336\064\245)BF)F)F)F)F)F)F)F)F)F)F)F)F)F)F)F)F)F)F)F)\253R\070\306\337"
  "\377\377\377\377\377\377\377\377\377\377\377\377\377\377\377\377\377\377"
  "\377\377\377\377\377\377\377\377\377\276\367\367\275jJF)F)F)F)F)F)F)F)F)"
  "F)F)F)F)F)F)F)F)U\255\276\367\377\377\377\377\377\377\337\377\373\336\226"
  "\265r\224\317{Mk\317{\222\224\226\265\373\336\377\377\377\377\377\377\377"
  "\377\236\367\364\234F)F)F)F)F)F)F)F)F)F)F)F)F)F)\010B\272\326\377\377\377"
  "\377\377\377}\357\064\245IJF)F)F)F)F)F)F)F)F)jJU\255\236\367\377\377\377\377"
  "\377\377y\316\307\071F)F)F)F)F)F)F)F)F)F)F)jJ\034\347\377\377\377\377\276\367"
  "u\255\247\061F)F)F)F)F)F)F)F)F)F)F)F)F)\350\071\266\265\337\377\377\377\377"
  "\377\373\336)BF)F)F)F)F)F)F)F)F)\350A\034\347\377\377\377\377}\357\216sF)"
  "F)F)F)F)F)F)F)F)F)F)F)F)F)F)F)F)\257s}\357\377\377\377\377\373\336\307\071"
  "F)F)F)F)F)F)F)F)\232\326\377\377\377\377\373\336IJF)F)F)F)F)F)F)F)F)F)F)"
  "F)F)F)F)F)F)F)F)\253R<\347\377\377\377\377Y\316F)F)F)F)F)F)F)\065\245\377"
  "\377\377\377]\357IJF)F)F)F)F)F)F)\222\224\232\326]\357}\357]\357\232\326"
  "\323\234f)F)F)F)F)F)F)\253Z\236\367\377\377\377\377\323\234F)F)F)F)F)\253"
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
  "\377\377\377\377\377\377\377\337\377\034\347u\255\212RF)F)F)F)F)F)F)F)F)F"
  ")F)F)F)F)F)F)F)F)F)F)F)F)F)F)F))B\020\204\064\245\226\265\266\265\226\265\064"
  "\245\020\204\010BF)F)F)F)F)F)F)F)F)F)F)F)F)F)"

};

Image IMAGE_QUESTION = {37, 37, (const uint16_t*)(data)};
