median-dispersion/GMT-Geiger-Counter/Firmware/GMT-Geiger-Counter/ImageRotate.cpp

#include "Graphics.h"

const PROGMEM uint8_t data[] = {

  "F)F)F)F)F)F)F)F)F)F)F)F)F)F)\247\071\024\245\020\204F)F)F)F)F)F)F)F)F)F)F)F"
  ")F)F)F)F)F)F)F)F)F)F)F)F)F)F)F)u\255\377\377\377\377\232\326-cF)F)F)F)F)"
  "F)F)F)F)F)F)F)F)F)F)F)F)F)F)F)F)F)F)F)F)\367\275\377\377\377\377\377\377"
  "\337\377\030\306IJF)F)F)F)F)F)F)F)F)F)F)F)F)F)F)F)F)F)F)F)F)F)F)\367\275\377"
  "\377\377\377\377\377\377\377\377\377\236\367\065\245F)F)F)F)F)F)F)F)F)F)F"
  ")F)F)F)F)F)F)F)\247\071q\214U\255\367\275<\347\377\377\377\377\377\377\377"
  "\377\377\377\377\377\377\377\034\347MkF)F)F)F)F)F)F)F)F)F)F)F)F)F)\060\204"
  "\232\326\276\367\377\377\377\377\377\377\377\377\377\377\377\377\377\377"
  "\377\377\377\377\377\377\377\377\377\377\232\326F)F)F)F)F)F)F)F)F)F)F)F)"
  "nk\272\326\377\377\377\377\377\377\377\377\377\377\377\377\377\377\377\377"
  "\377\377\377\377\377\377\377\377\377\377\377\377\377\377\024\245F)F)F)F)F"
  ")F)F)F)F)F)F)\262\224\337\377\377\377\377\377\377\377\373\336u\255\317{\253"
  "R\367\275\377\377\377\377\377\377\377\377\377\377\377\377\373\336\216sF)"
  "F)F)F)F)F)F)F)F)F)F)u\255\377\377\377\377\377\377\333\336\256sF)F)F)F)\367"
  "\275\377\377\377\377\377\377\377\377}\357\262\224F)F)F)F)F)F)F)F)F)F)F)F"
  ")\262\224\377\377\377\377\377\377U\255F)F)F)F)F)F)\327\275\377\377\377\377"
  "\337\377\226\265F)F)F)F)F)F)F)F)F)F)F)F)F)nk\337\377\377\377\377\377r\214"
  "F)F)F)F)F)F)F)-c\373\336Y\316\313ZF)F)F)F)F)F)F)F)F)F)F)F)F)F)\272\326\377"
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
  ")F)F)F)\020\204\232\326\276\367\377\377\377\377\377\377Y\316F)F)F)F)F)F)F"
  ")F)F)F)F)F)F)F)F)F)F)F)F)F)F)F)F)F)F)\247\061q\214U\255\367\275\317{F)F)F"
  ")F)F)F)F)F)F)F)F)F)F)F)F)"

};

Image IMAGE_ROTATE = {30, 33, (const uint16_t*)(data)};
