median-dispersion/GMT-Geiger-Counter/Firmware/GMT-Geiger-Counter/ImageDecreaseDown.cpp

#include "Graphics.h"

const PROGMEM uint8_t data[] = {

  "\314Z\360{\360{\360{\360{\360{\360{\360{\360{\360{\314Z\061\204\377\377\377"
  "\377\377\377\377\377\377\377\377\377\377\377\377\377\377\377Q\214\314Z\266"
  "\265\377\377\377\377\377\377\377\377\377\377\377\377\377\377\226\265\314"
  "Z\314Z\314Z\266\265\377\377\377\377\377\377\377\377\377\377\226\265\314Z"
  "\314Z\314Z\314Z\314Z\266\265\377\377\377\377\377\377\226\265\314Z\314Z\314"
  "Z\314Z\314Z\314Z\314Z\266\265\377\377\226\265\314Z\314Z\314Z\314Z\314Z\314"
  "Z\314Z\314Z\314Znk\314Z\314Z\314Z\314Z\314Z"

};

Image IMAGE_DECREASE_DOWN = {11, 7, (const uint16_t*)(data)};
