median-dispersion/GMT-Geiger-Counter/Firmware/GMT-Geiger-Counter/ScreenDisplaySettings.cpp

#include "ScreenDisplaySettings.h"

//-------------------------------------------------------------------------------------------------
// Public

// ================================================================================================
// Constructor
// ================================================================================================
ScreenDisplaySettings::ScreenDisplaySettings():

  // Initialize members
  ScreenBasicLandscape(STRING_DISPLAY_SETTINGS),
  display(0, STRING_DISPLAY,      true),
  timeout(1, STRING_AUTO_TIMEOUT, true),
  rgbLED( 2, STRING_RGB_LED,      true)

{}

// ================================================================================================
// Update
// ================================================================================================
void ScreenDisplaySettings::update(const XPT2046::Point &position) {

  // Update the basic screen
  ScreenBasicLandscape::update(position);

  // Update screen elements
  display.update(position);
  timeout.update(position);
  rgbLED.update(position);

}

// ================================================================================================
// Draw
// ================================================================================================
void ScreenDisplaySettings::draw(GFXcanvas16 &canvas) {

  // Draw the basic screen
  ScreenBasicLandscape::draw(canvas);

  // Draw screen elements
  display.draw(canvas);
  timeout.draw(canvas);
  rgbLED.draw(canvas);

}
