median-dispersion/GMT-Geiger-Counter/Firmware/GMT-Geiger-Counter/ScreenBasicLandscape.h

#ifndef _SCREEN_BASIC_H
#define _SCREEN_BASIC_H

#include "Arduino.h"
#include "Adafruit_GFX.h"
#include "XPT2046.h"
#include "Graphics.h"
#include "Screen.h"
#include "TouchIcon.h"

class ScreenBasicLandscape: public Screen {

  //-----------------------------------------------------------------------------------------------
  // Public

  public:

    // Screen elements
    TouchIcon back;

    // Constructor
    ScreenBasicLandscape(const char *title);

    // Update and draw calls
    void update(const XPT2046::Point &position) override;
    void draw(GFXcanvas16 &canvas) override;

  //-----------------------------------------------------------------------------------------------
  // Private
  
  private:

    // Screen title
    const char *_title;

};

#endif
