median-dispersion/GMT-Geiger-Counter/Firmware/GMT-Geiger-Counter/ScreenCosmicRayDetector.h

#ifndef _SCREEN_COSMIC_RAY_DETECTOR_H
#define _SCREEN_COSMIC_RAY_DETECTOR_H

#include "Arduino.h"
#include "Adafruit_GFX.h"
#include "XPT2046.h"
#include "Strings.h"
#include "Graphics.h"
#include "ScreenBasicPortrait.h"
#include "DisplayDoseScreen.h"
#include "DisplayInfoBox.h"
#include "DisplayToastBox.h"

class ScreenCosmicRayDetector: public ScreenBasicPortrait {

  //-----------------------------------------------------------------------------------------------
  // Public
  
  public:

    // Screen elements
    TouchIcon mute;
    TouchIcon sleep;

    // Constructor
    ScreenCosmicRayDetector();

    // Update and draw calls
    void update(const XPT2046::Point &position) override;
    void draw(GFXcanvas16 &canvas) override;

    // Set screen variables
    void setCoincidenceEvents(const uint64_t &coincidenceEvents);               // Set coincidence events
    void setCoincidenceEventsPerHour(const uint32_t &coincidenceEventsPerHour); // Set the coincidence events per hour value
    void setCoincidenceEventsTotal(const uint64_t &coincidenceEventsTotal);     // Set the total number of coincidence events
    void setMainTubeCounts(const uint64_t &mainTubeCounts);                     // Set main tube counts
    void setFollowerTubeCounts(const uint64_t &followerTubeCounts);             // Set follower tube counts

  // ----------------------------------------------------------------------------------------------
  // Private

  private:

    String            _coincidenceEventsString;        // Coincidence events string
    String            _coincidenceEventsPerHourString; // Coincidence events per hour string
    String            _coincidenceEventsTotalString;   // Total Coincidence events string
    String            _mainTubeCountsString;           // Main tube counts string
    String            _followerTubeCountsString;       // Follower tube counts string
    DisplayDoseScreen _coincidenceEventsScreen;        // Coincidence events screen
    DisplayInfoBox    _coincidenceEventsPerHour;       // Coincidence events per hour
    DisplayInfoBox    _coincidenceEventsTotal;         // Total number of coincidence events since power on
    DisplayToastBox   _mainTubeCounts;                 // Main tube counts
    DisplayToastBox   _followerTubeCounts;             // Follower tube counts

};

#endif
