median-dispersion/GMT-Geiger-Counter/Firmware/GMT-Geiger-Counter/TouchToggle.h

#ifndef _TOUCH_TOGGLE_H
#define _TOUCH_TOGGLE_H

#include "Arduino.h"
#include "Adafruit_GFX.h"
#include "XPT2046.h"
#include "Graphics.h"

class TouchToggle {

  //-----------------------------------------------------------------------------------------------
  // Public

  public:

    // Constructor
    TouchToggle(const uint8_t row, const char *text, const bool toggled);

    void update(const XPT2046::Point &position); // Update the touch toggle with the touch position
    void draw(GFXcanvas16 &canvas);              // Draw the touch toggle to the frame buffer
    void (*action)(const bool toggled);          // Function pointer to execute a function on touchdown
    void toggleOn();                             // Toggle on
    void toggleOff();                            // Toggle off
    void toggle();                               // Toggle state
    void setToggleState(const bool toggled);     // Toggle a specific state
    bool getToggleState();                       // Return the toggle state

  //-----------------------------------------------------------------------------------------------
  // Private

  private:

    const uint16_t _y;       // Y position
    const char     *_text;   // Toggle text
    bool           _toggled; // Toggle state

};

#endif
