median-dispersion/GMT-Geiger-Counter/Firmware/GMT-Geiger-Counter/DisplayToastBox.cpp

#include "DisplayToastBox.h"

// ------------------------------------------------------------------------------------------------
// Public

// ================================================================================================
// Constructor
// ================================================================================================
DisplayToastBox::DisplayToastBox(const uint16_t x, const uint16_t y, const uint16_t width, const char *title, const char *value):

  // Initialize members
  _x(x),
  _y(y),
  _width(width),
  _title(title),
  _value(value)

{}

// ================================================================================================
// Draw the toast box
// ================================================================================================
void DisplayToastBox::draw(GFXcanvas16 &canvas) {

  // Draw background
  canvas.fillRect(_x, _y, _width, 51, COLOR_GRAY_DARK);

  // Set the font family, size and color
  canvas.setFont(&FreeSans9pt7b);
  canvas.setTextColor(COLOR_GRAY_LIGHT);

  // Draw title
  canvas.setCursor(_x + 5, _y + 20);
  canvas.print(_title);

  // Set the font family, size and color
  canvas.setFont(&FreeSansBold9pt7b);
  canvas.setTextColor(COLOR_WHITE);

  // Draw title
  canvas.setCursor(_x + 5, _y + 42);
  canvas.print(_value);

}

// ================================================================================================
// Set the toast box value
// ================================================================================================
void DisplayToastBox::setValue(const char *value) {

  _value = value;

}
