median-dispersion/GMT-Geiger-Counter/Firmware/GMT-Geiger-Counter/ImageAverage.cpp

#include "Graphics.h"

const PROGMEM uint8_t data[] = {

  "F)F)F)F)\216sq\214,cF)F)nk\307\071F)F)\060\204]\357\276\367]\357\337\377<\347"
  "\226\265\337\377nkF)\060\204\337\377\226\265\207\061F)\247\061\232\326\377\377"
  "\226\265F)F)]\357\226\265F)F)F)\262\224\337\377\232\326<\347F)\216s\276\367"
  "\207\061F)F)\262\224\337\377\262\224\307\071\337\377\014cq\214]\357F)F)\262"
  "\224\337\377\262\224F)F)]\357q\214,c\337\377\247\061\262\224\337\377\262\224"
  "F)F)\247\061\276\367\216sF)<\347\232\326\337\377\262\224F)F)F)\266\265]\357"
  "F)F)\226\265\377\377\232\326\307\071F)\247\061\266\265\337\377\020\204F)nk\337"
  "\377\226\265<\347\337\377]\357\337\377]\357\020\204F)F)\310\071nkF)F)\014cq"
  "\214nkF)F)F)F)"

};

Image IMAGE_AVERAGE = {11, 11, (const uint16_t*)(data)};
