median-dispersion/GMT-Geiger-Counter/Firmware/GMT-Geiger-Counter/ImageBack.cpp

#include "Graphics.h"

const PROGMEM uint8_t data[] = {

  "\314Z\314Z\314Z\314Z\314Z\314Z\314Znk\020\204\314Z\314Z\314Z\314Z\314Z\314"
  "Z\266\265\276\367\373\336\314Z\314Z\314Z\314Z\222\224]\357\377\377\377\377"
  "\374\336\314Z\314Z\317{\272\326\377\377\377\377\377\377\377\377\374\336-"
  "c\370\275\337\377\377\377\377\377\377\377\377\377\377\377\374\336y\316\377"
  "\377\377\377\377\377\377\377\377\377\377\377\377\377\374\336-c\370\275\337"
  "\377\377\377\377\377\377\377\377\377\377\377\374\336\314Z\314Z\317{\272\326"
  "\377\377\377\377\377\377\377\377\374\336\314Z\314Z\314Z\314Z\222\224=\347"
  "\377\377\377\377\374\336\314Z\314Z\314Z\314Z\314Z\314Z\266\265\276\367\373"
  "\336\314Z\314Z\314Z\314Z\314Z\314Z\314ZNk\317{"

};

Image IMAGE_BACK = {9, 11, (const uint16_t*)(data)};
