median-dispersion/GMT-Geiger-Counter/Firmware/GMT-Geiger-Counter/ImageClock.cpp

#include "Graphics.h"

const PROGMEM uint8_t data[] = {

  "F)F)F)F)\262\224\232\326}\357\276\367}\357\232\326\222\224F)F)F)F)F)F)\354"
  "Z\034\347\377\377\377\377\377\377\377\377\377\377\377\377\377\377\034\347\354"
  "ZF)F)F)\354Z\236\367\377\377\377\377\377\377\377\377\377\377\377\377\377"
  "\377\377\377\377\377\236\367\313ZF)F)\034\347\377\377\377\377\377\377\377"
  "\377\377\377f)\377\377\377\377\377\377\377\377\377\377\373\336F)\262\224"
  "\377\377\377\377\377\377\377\377\377\377\377\377F)\377\377\377\377\377\377"
  "\377\377\377\377\377\377\222\224\232\326\377\377\377\377\377\377\377\377"
  "\377\377\377\377F)\377\377\377\377\377\377\377\377\377\377\377\377\232\326"
  "}\357\377\377\377\377\377\377\377\377\377\377\377\377F)\377\377\377\377\377"
  "\377\377\377\377\377\377\377}\357\276\367\377\377\377\377\377\377\377\377"
  "\377\377\377\377f)\373\336\377\377\377\377\377\377\377\377\377\377\276\367"
  "}\357\377\377\377\377\377\377\377\377\377\377\377\377\373\336f)\333\336\377"
  "\377\377\377\377\377\377\377}\357\232\326\377\377\377\377\377\377\377\377"
  "\377\377\377\377\377\377\373\336f)\034\347\377\377\377\377\377\377\232\326"
  "\222\224\377\377\377\377\377\377\377\377\377\377\377\377\377\377\377\377"
  "\034\347f)\377\377\377\377\377\377\222\224F)\034\347\377\377\377\377\377\377"
  "\377\377\377\377\377\377\377\377\377\377\377\377\377\377\377\377\373\336"
  "F)F)\354Z\236\367\377\377\377\377\377\377\377\377\377\377\377\377\377\377"
  "\377\377\377\377\236\367\313ZF)F)F)\313Z\373\336\377\377\377\377\377\377"
  "\377\377\377\377\377\377\377\377\373\336\313ZF)F)F)F)F)F)\222\224\232\326"
  "}\357\276\367}\357\232\326\222\224F)F)F)F)"

};

Image IMAGE_CLOCK = {15, 15, (const uint16_t*)(data)};
