median-dispersion/GMT-Geiger-Counter/Firmware/GMT-Geiger-Counter/ImageMaximum.cpp

#include "Graphics.h"

const PROGMEM uint8_t data[] = {

  "F)F)F)F)U\255\377\377u\255F)F)F)F)F)F)F)U\255\276\367\065\245\276\367U\255"
  "F)F)F)F)F)U\255\276\367\020\204F)\357{\276\367u\255F)F)F)U\255\276\367\020"
  "\204F)F)F)\357{\276\367u\255F)\216s\276\367\360{F)F)F)F)F)\360{\276\367\317"
  "{"

};

Image IMAGE_MAXIMUM = {11, 5, (const uint16_t*)(data)};
