median-dispersion/GMT-Geiger-Counter/Firmware/GMT-Geiger-Counter/ImageMute.cpp

#include "Graphics.h"

const PROGMEM uint8_t data[] = {

  "\034\347\024\245\314Z\314Z\314Z\314Z\314Z\314Z\314Z\314Z\314Z\314Z\314Z\314"
  "Z\314Z\364\234\337\377\064\245\314Z\314Z\314Z\314Z\314Z\314Z\314Z\314Z\314"
  "Z\314Z\314Z\314Z\314Z\024\245\337\377\024\245\314Z\314Z\314ZQ\214\314Z\314"
  "Z\314Z\314Z\314Z\314Z\314Z\314Z\314Z\024\245\337\377\024\245\314Z\232\326\377"
  "\377\015c\034\347Y\316\015c\314Z\314Z\314Z\314Z\314Z\217s\024\245\337\377\024"
  "\245\364\234\377\377\015c\020\204\034\347\373\336\314Z\314Z\314Z\314Z\314Z<"
  "\347\364\234\024\245\337\377\024\245\364\234\015c\024\245nk}\357\065\245\314Z"
  "\314Z\314Z\314Z]\357\377\377\364\234\024\245\337\377\024\245\314Z\276\367\327"
  "\275\327\275\333\336\314Z\314Z\314Z\314Z]\357\377\377\377\377\364\234\024"
  "\245\337\377\024\245\364\234\232\326\024\245<\347\314Z\314Z\314Z\314Z]\357"
  "\377\377\377\377\377\377\364\234\024\245\337\377\024\245Nk\327\275\333\336"
  "\314Z\314Z\314Z\314Z]\357\377\377\377\377\377\377\377\377\364\234\024\245"
  "\337\377\024\245\364\234\024\245\314Z\314Z\314Z\314Z\323\234\266\265\266\265"
  "}\357\377\377\377\377\015c\024\245\337\377\024\245\314Z\314Z\314Z\314Z\314Z"
  "\314Z\314Z\314Z-c\273\326\377\377\015c\314Z\024\245\337\377\024\245\314Z\314"
  "Z\314Z\314Z\314Z\314Z\314Z\314Z\314ZQ\214\314Z\314Z\314Z\024\245\337\377\024"
  "\245\314Z\314Z\314Z\314Z\314Z\314Z\314Z\314Z\314Z\314Z\314Z\314Z\314Z\364"
  "\234\337\377\064\245\314Z\314Z\314Z\314Z\314Z\314Z\314Z\314Z\314Z\314Z\314"
  "Z\314Z\314Z\024\245\034\347"

};

Image IMAGE_MUTE = {15, 15, (const uint16_t*)(data)};
