median-dispersion/GMT-Geiger-Counter/Firmware/GMT-Geiger-Counter/ImageNext.cpp

#include "Graphics.h"

const PROGMEM uint8_t data[] = {

  "\020\204Nk\314Z\314Z\314Z\314Z\314Z\314Z\314Z\373\336\276\367\266\265\314"
  "Z\314Z\314Z\314Z\314Z\314Z\374\336\377\377\377\377]\357\323\234\314Z\314"
  "Z\314Z\314Z\374\336\377\377\377\377\377\377\377\377\373\336\020\204\314Z\314"
  "Z\374\336\377\377\377\377\377\377\377\377\377\377\337\377Y\316Nk\374\336"
  "\377\377\377\377\377\377\377\377\377\377\377\377\377\377y\316\374\336\377"
  "\377\377\377\377\377\377\377\377\377\337\377Y\316Nk\374\336\377\377\377\377"
  "\377\377\377\377\373\336\020\204\314Z\314Z\374\336\377\377\377\377]\357\323"
  "\234\314Z\314Z\314Z\314Z\373\336\276\367\266\265\314Z\314Z\314Z\314Z\314"
  "Z\314Z\317{Nk\314Z\314Z\314Z\314Z\314Z\314Z\314Z"

};

Image IMAGE_NEXT = {9, 11, (const uint16_t*)(data)};
