median-dispersion/GMT-Geiger-Counter/Firmware/GMT-Geiger-Counter/ImageParticle.cpp

#include "Graphics.h"

const PROGMEM uint8_t data[] = {

  "F)F)F)F)\216s\222\224\216sF)F)F)F)F)F)\060\204]\357\377\377\377\377\377\377"
  "]\357\060\204F)F)F)\060\204\377\377\377\377\377\377\377\377\377\377\377\377"
  "\377\377\060\204F)F)]\357\377\377\377\377\377\377\377\377\377\377\377\377"
  "\377\377]\357F)\216s\377\377\377\377\377\377\377\377\377\377\377\377\377"
  "\377\377\377\377\377\216sr\214\377\377\377\377\377\377\377\377\377\377\377"
  "\377\377\377\377\377\377\377r\214\216s\377\377\377\377\377\377\377\377\377"
  "\377\377\377\377\377\377\377\377\377\216sF)]\357\377\377\377\377\377\377"
  "\377\377\377\377\377\377\377\377]\357F)F)\060\204\337\377\377\377\377\377"
  "\377\377\377\377\377\377\337\377\020\204F)F)F)\020\204]\357\377\377\377\377"
  "\377\377]\357\020\204F)F)F)F)F)F)\216sr\214nkF)F)F)F)"

};

Image IMAGE_PARTICLE = {11, 11, (const uint16_t*)(data)};
