median-dispersion/GMT-Geiger-Counter/Firmware/GMT-Geiger-Counter/ImageRadiation.cpp

#include "Graphics.h"

const PROGMEM uint8_t data[] = {

  "F)F)\313Zy\316\354ZF)F)F)F)F)\354Z\232\326\313ZF)F)F)\313Z}\357\377\377y"
  "\316F)F)F)F)F)y\316\377\377}\357\354ZF)F)\373\336\377\377\377\377\377\377"
  "\020\204F)F)F)\020\204\377\377\377\377\377\377\373\336F)Q\214\377\377\377\377"
  "\377\377\377\377\034\347F)F)F)\034\347\377\377\377\377\377\377\377\377q\214"
  "\232\326\377\377\377\377\377\377\377\377\034\347F))BF)\373\336\377\377\377"
  "\377\377\377\377\377\232\326]\357\377\377\377\377\377\377\377\377\014c\272"
  "\326\377\377\272\326\014c\377\377\377\377\377\377\377\377}\357U\255\030\306"
  "\030\306\030\306U\255)B\377\377\377\377\377\377)BU\255\030\306\030\306\030\306"
  "U\255F)F)F)F)F)F)\272\326\377\377\232\326F)F)F)F)F)F)F)F)F)F)F)F)\207\061"
  ")BF)F)F)F)F)F)F)F)F)F)F)F)Q\214\377\377\236\367\377\377Q\214F)F)F)F)F)F)"
  "F)F)F)f)<\347\377\377\377\377\377\377]\357f)F)F)F)F)F)F)F)F)U\255\377\377"
  "\377\377\377\377\377\377\377\377U\255F)F)F)F)F)F)F)F)\236\367\377\377\377"
  "\377\377\377\377\377\377\377\236\367F)F)F)F)F)F)F)F)q\214y\316]\357\276\367"
  "]\357y\316q\214F)F)F)F)"

};

Image IMAGE_RADIATION = {15, 14, (const uint16_t*)(data)};
