median-dispersion/GMT-Geiger-Counter/Firmware/GMT-Geiger-Counter/ImageSleepSmall.cpp

#include "Graphics.h"

const PROGMEM uint8_t data[] = {

  "\314Z\314Z\314Z\314Z\314Z\314Z\314Z\314Z\314Z\314Z\061\204\034\347\034\347\034"
  "\347\232\326\314Z\314Z\314Z\314Z\314Z\314Z\314Z\314Z\314Z\314Z-c\065\245\030"
  "\306\377\377\327\275\314Z\314Z\314Z\314Z\314Z\064\245\232\326\232\326\232"
  "\326\065\245\314Z\061\204\276\367\327\275\314Z\314Z\314Z\314Z\314Z\314Zr\214"
  "\370\275\034\347\377\377\363\234\360{\276\367\236\367Y\316\327\275\226\265"
  "\370\275\370\275\370\275\257s\314Z\024\245\337\377\024\245\314Z\257s\070\306"
  "Y\316Y\316\266\265\327\275Y\316\236\367\276\367\360{\363\234\377\377\034\347"
  "\370\275r\214\314Z\314Z\314Z\314Z\314Z\314Z\327\275\276\367\061\204\314Z\065"
  "\245\232\326\232\326\232\326\064\245\314Z\314Z\314Z\314Z\314Z\327\275\377"
  "\377\030\306\065\245-c\314Z\314Z\314Z\314Z\314Z\314Z\314Z\314Z\314Z\314Z\232"
  "\326\034\347\034\347\034\347\061\204\314Z\314Z\314Z\314Z\314Z\314Z\314Z\314Z"
  "\314Z\314Z"

};

Image IMAGE_SLEEP_SMALL = {15, 9, (const uint16_t*)(data)};
