median-dispersion/GMT-Geiger-Counter/Firmware/GMT-Geiger-Counter/ImageSum.cpp

#include "Graphics.h"

const PROGMEM uint8_t data[] = {

  "\272\326\337\377\337\377\337\377\337\377\337\377\337\377\337\377\337\377"
  "\337\377\333\336\323\234\377\377\377\377\226\265mkmkmkmkmk\024\245]\357F)"
  "y\316\377\377\276\367\253RF)F)F)F)-c\327\275F))B}\357\377\377\333\336F)F"
  ")F)F)F)F)F)F)\061\204\377\377\377\377\064\245F)F)F)F)F)F)F)F)\030\306\377\377"
  "\337\377-cF)F)F)F)F)F)F)\310\071]\357\377\377Y\316F)F)F)F)F)F)F)F)\363\234"
  "\377\377\317{F)F)F)F)F)F)F)\310\071]\357\266\265F)F)F)F)F)F)F)F)\030\306\034"
  "\347\207\061F)F)F)F)F)F)F)\061\204\337\377MkF)F)F)F)F)F)F)IJ\236\367U\255F"
  ")F)F)F)F)Mk\030\306F)y\316]\357\020\204\020\204\020\204\020\204\020\204\020\204"
  "u\255]\357\323\234\377\377\377\377\377\377\377\377\377\377\377\377\377\377"
  "\377\377\377\377]\357\272\326\337\377\337\377\337\377\337\377\337\377\337"
  "\377\337\377\337\377\337\377\273\326"

};

Image IMAGE_SUM = {11, 15, (const uint16_t*)(data)};
